Squantor/squantorDevelBoards/electronics/nuclone_STM32F031K6/README.md

# Nuclone development board for STM32F030K6
STM32F031K6 development board inspired by the nucleo series from STM32.
## TODO's
Still some things need to be done:
* schematic entry (WIP)
* PCB layout (Done)
* Review with one night in between (Done)
* Produce at [JLCPCB](https://jlcpcb.com/) (Done)
* Assemble (Done)
* Test & characterise (WIP)
* update Readme.md with pictures and BOM (WIP)
