Squantor/squantorDevelBoards/mechanical/small_nuclone_base_plate/README.md

# Small nuclone board box base plate
Base plate to mount the nuclone board on.
## Variants
* binding post holes for m3 screws
* binding post holes for m3 threaded inserts
## Pictures
TODO
