Squantor/squantorDevelBoards/electronics/nuclone_LPC1125JBD48-303/README.md

# Nuclone development board for LPC1125JBD48/303
LPC1125JBD48 development board inspired by the nucleo series from STM32.
## TODO's
Still some things need to be done:
* schematic entry (WIP)
* PCB layout (WIP)
* Review with one night in between (TODO)
* Produce at [JLCPCB](https://jlcpcb.com/) (TODO)
* Assemble (TODO)
* Test & characterise (TODO)
* update Readme.md with pictures and BOM (TODO)
