Squantor/squantorDevelBoards/software/cobalt_ant/README.md

# cobalt ant bringup
This is the bringup and test code for the cobalt ant datalogger. 
## TODO
* remove dependency on stdio and string libraries
* Some hardware pin definitions/libraries needed
