Squantor/squantorDevelBoards/electronics/nuclone_tester_medium/README.md

# Nuclone tester for medium sized boards
Test jig for the Medium sized nuclone boards.
## TODO's
Still some things need to be done:
* schematic entry (Done)
* PCB layout (Done)
* Review with one night in between (Wip)
* Produce at [JLCPCB](https://jlcpcb.com/) (TODO)
* Assemble (TODO)
* Test & characterise (TODO)
* update Readme.md with pictures and BOM (TODO)
