Squantor/squantorDevelBoards/electronics/nuclone_LPC804M101JHI33/nuclone_LPC804M101JHI33.kicad_pcb

## KiCad design electronics/nuclone_LPC804M101JHI33/nuclone_LPC804M101JHI33.kicad_pcb (2022-09-12)

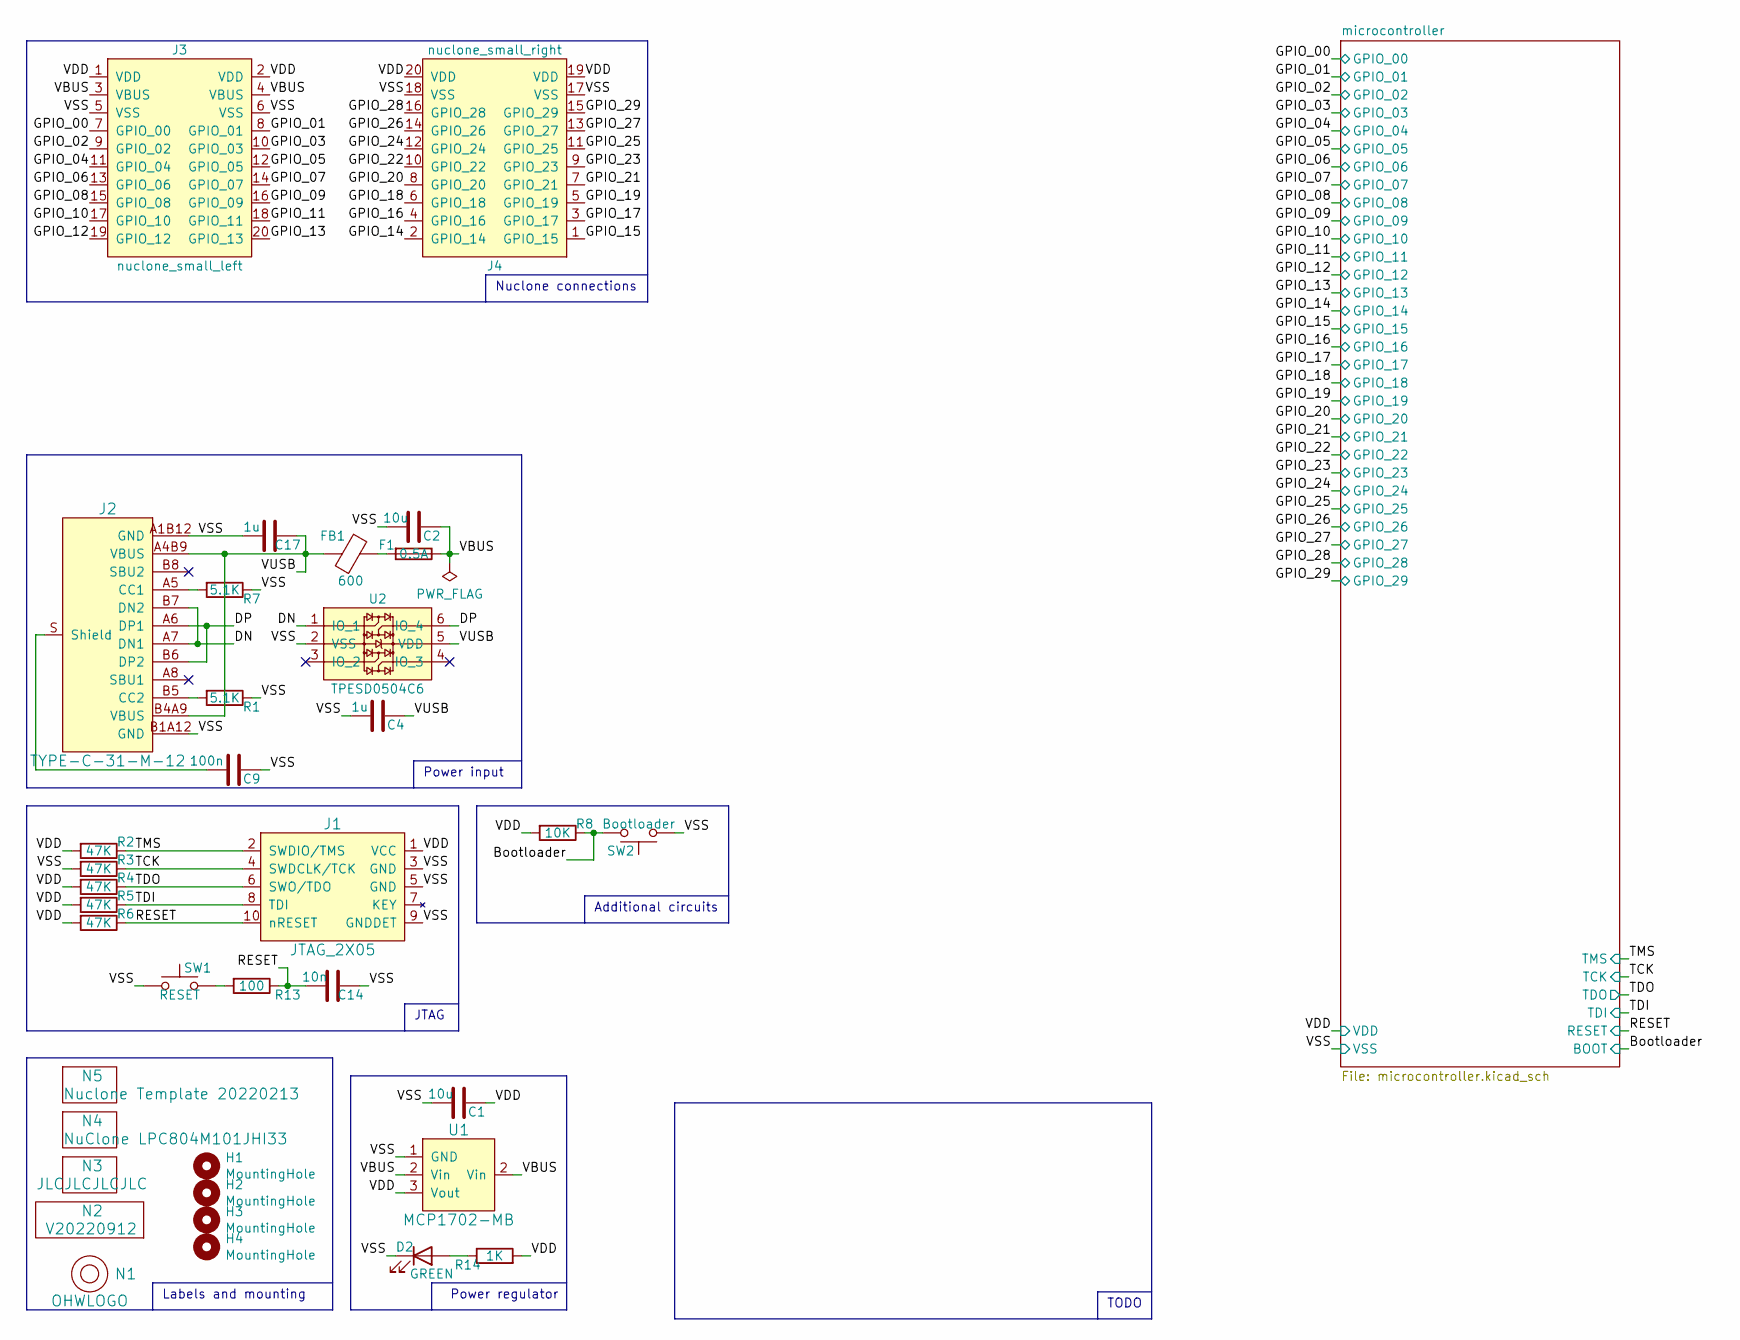
[picture p26: schematic nuclone_LPC804M101JHI33.kicad_sch]

Parts:
C1, C2: 10u; C_0603
C4: 1u; C_0402
C9: 100n; C_0805
C14: 10n; C_0402
C17: 1u; C_0603
D2: GREEN; LED_0603_hand
F1: 0.5A; F_0603_hand
FB1: 600; L_0603
H1, H2, H3, H4: MountingHole; MountingHole_3.2mm_M3_Pad_Via
J1: JTAG_2X05; Header-0127-2X05-H006
J2: TYPE-C-31-M-12; USB-C-HRO-31-M-12
J3: nuclone_small_left; nuclone_small_left_stacked
J4: nuclone_small_right; nuclone_small_right_stacked
N1: OHWLOGO; OSHW-Symbol_6.7x6mm_SilkScreen
N2: V20220912; Label_Generic
N3: JLCJLCJLCJLC; Label_Generic
N4: NuClone LPC804M101JHI33; Label_Generic
N5: Nuclone Template 20220213; Label_Generic
R1, R7: 5.1K; R_0402_hand
R2, R3, R4, R5, R6: 47K; R_0402_hand
R8: 10K; R_0402_hand
R13: 100; R_0402_hand
R14: 1K; R_0402_hand
SW1: RESET; TD-85XU
SW2: Bootloader; TD-85XU
U1: MCP1702-MB; SOT89-NXP
U2: TPESD0504C6; SOT363-ONsemi

Connections:
/Bootloader: R8.1, SW2.2; also elsewhere on the board
/DN: J2.A7 (DN1), J2.B7 (DN2), U2.1 (IO_1)
/DP: J2.A6 (DP1), J2.B6 (DP2), U2.6 (IO_4)
/GPIO_00: J3.7 (GPIO_00); also elsewhere on the board
/GPIO_01: J3.8 (GPIO_01); also elsewhere on the board
/GPIO_02: J3.9 (GPIO_02); also elsewhere on the board
/GPIO_03: J3.10 (GPIO_03); also elsewhere on the board
/GPIO_04: J3.11 (GPIO_04); also elsewhere on the board
/GPIO_05: J3.12 (GPIO_05); also elsewhere on the board
/GPIO_06: J3.13 (GPIO_06); also elsewhere on the board
/GPIO_07: J3.14 (GPIO_07); also elsewhere on the board
/GPIO_08: J3.15 (GPIO_08); also elsewhere on the board
/GPIO_09: J3.16 (GPIO_09); also elsewhere on the board
/GPIO_10: J3.17 (GPIO_10); also elsewhere on the board
/GPIO_11: J3.18 (GPIO_11); also elsewhere on the board
/GPIO_12: J3.19 (GPIO_12); also elsewhere on the board
/GPIO_13: J3.20 (GPIO_13); also elsewhere on the board
/GPIO_14: J4.2 (GPIO_14); also elsewhere on the board
/GPIO_15: J4.1 (GPIO_15); also elsewhere on the board
/GPIO_16: J4.4 (GPIO_16); also elsewhere on the board
/GPIO_17: J4.3 (GPIO_17); also elsewhere on the board
/GPIO_18: J4.6 (GPIO_18); also elsewhere on the board
/GPIO_19: J4.5 (GPIO_19); also elsewhere on the board
/GPIO_20: J4.8 (GPIO_20); also elsewhere on the board
/GPIO_21: J4.7 (GPIO_21); also elsewhere on the board
/GPIO_22: J4.10 (GPIO_22); also elsewhere on the board
/GPIO_23: J4.9 (GPIO_23); also elsewhere on the board
/GPIO_24: J4.12 (GPIO_24); also elsewhere on the board
/GPIO_25: J4.11 (GPIO_25); also elsewhere on the board
/GPIO_26: J4.14 (GPIO_26); also elsewhere on the board
/GPIO_27: J4.13 (GPIO_27); also elsewhere on the board
/GPIO_28: J4.16 (GPIO_28); also elsewhere on the board
/GPIO_29: J4.15 (GPIO_29); also elsewhere on the board
/RESET: C14.2, J1.10 (nRESET), R6.1, R13.1; also elsewhere on the board
/TCK: J1.4 (SWDCLK/TCK), R3.1; also elsewhere on the board
/TDI: J1.8 (TDI), R5.1
/TDO: J1.6 (SWO/TDO), R4.1
/TMS: J1.2 (SWDIO/TMS), R2.1; also elsewhere on the board
/VBUS: C2.2, F1.1, J3.3 (VBUS), J3.4 (VBUS), U1.2 (Vin)
/VDD: C1.1, J1.1 (VCC), J3.1 (VDD), J3.2 (VDD), J4.19 (VDD), J4.20 (VDD), R2.2, R4.2, R5.2, R6.2, R8.2, R14.2, U1.3 (Vout); also elsewhere on the board
/VSS: C1.2, C2.1, C4.2, C9.1, C14.1, C17.1, D2.1 (K), J1.3 (GND), J1.5 (GND), J1.9 (GNDDET), J2.A1B12 (GND), J2.B1A12 (GND), J3.5 (VSS), J3.6 (VSS), J4.17 (VSS), J4.18 (VSS), R1.1, R3.2, R7.1, SW1.1, SW2.1, U1.1 (GND), U2.2 (VSS); also elsewhere on the board
/VUSB: C4.1, C17.2, FB1.2, J2.A4B9 (VBUS), J2.B4A9 (VBUS), U2.5 (VDD)
unnamed: C9.2, J2.S (Shield)
unnamed: D2.2 (A), R14.1
unnamed: F1.2, FB1.1
unnamed: J2.A5 (CC1), R7.2
unnamed: J2.B5 (CC2), R1.2
unnamed: R13.2, SW1.2

Notes on the sheet:
Power input
Labels and mounting
Additional circuits
Nuclone connections
JTAG
TODO
Power regulator

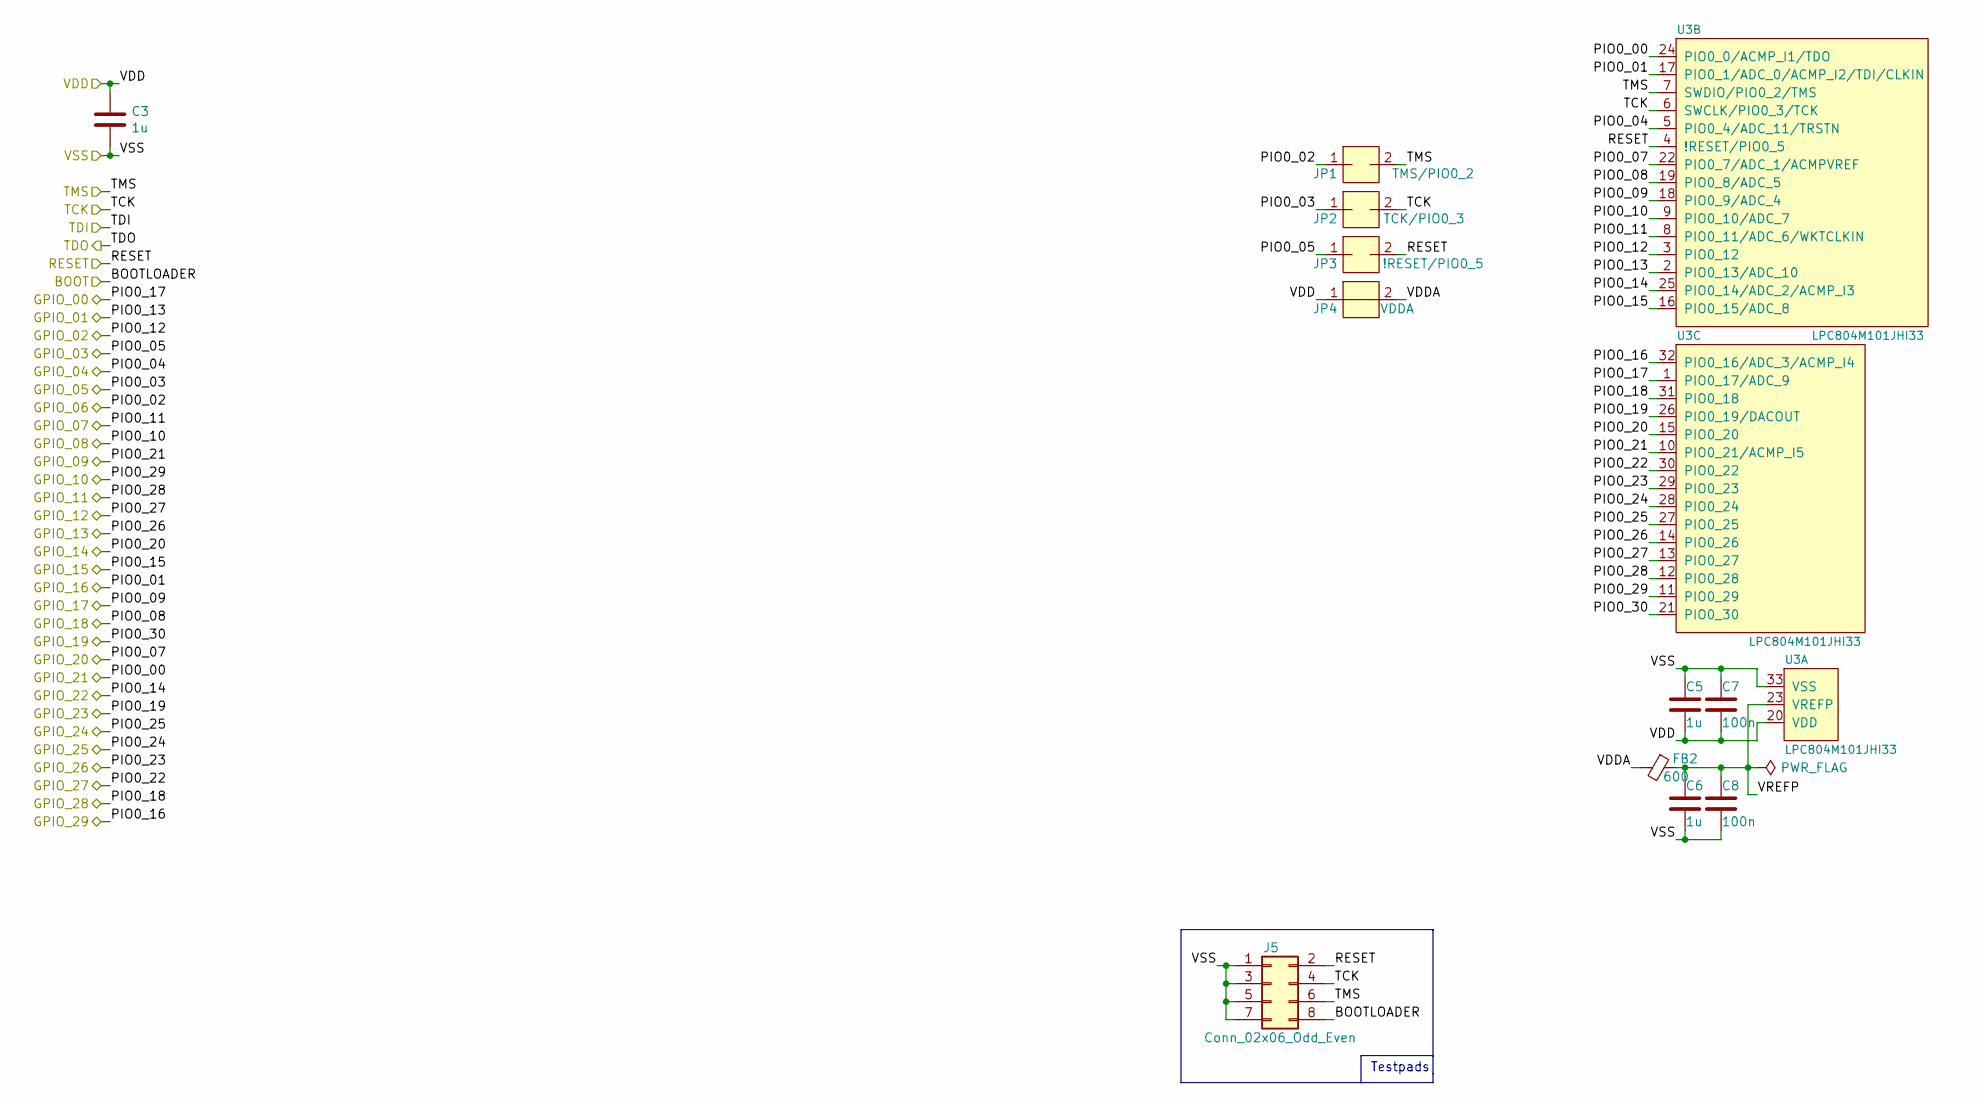
[picture p27: schematic microcontroller.kicad_sch]

Parts:
C3, C5, C6: 1u; C_0402
C7, C8: 100n; C_0402
FB2: 600; L_0402
J5: Conn_02x06_Odd_Even; Header-0127-2X04-H006
JP1: TMS/PIO0_2; solder_jumper_0402_2way_noconn
JP2: TCK/PIO0_3; solder_jumper_0402_2way_noconn
JP3: !RESET/PIO0_5; solder_jumper_0402_2way_noconn
JP4: VDDA; solder_jumper_0402_2way_conn
U3: LPC804M101JHI33; SOT617-3_alt_paste

Connections:
/Bootloader: J5.8; also elsewhere on the board
/GPIO_00: U3.1 (PIO0_17/ADC_9); also elsewhere on the board
/GPIO_01: U3.2 (PIO0_13/ADC_10); also elsewhere on the board
/GPIO_02: U3.3 (PIO0_12); also elsewhere on the board
/GPIO_03: JP3.1; also elsewhere on the board
/GPIO_04: U3.5 (PIO0_4/ADC_11/TRSTN); also elsewhere on the board
/GPIO_05: JP2.1; also elsewhere on the board
/GPIO_06: JP1.1; also elsewhere on the board
/GPIO_07: U3.8 (PIO0_11/ADC_6/WKTCLKIN); also elsewhere on the board
/GPIO_08: U3.9 (PIO0_10/ADC_7); also elsewhere on the board
/GPIO_09: U3.10 (PIO0_21/ACMP_I5); also elsewhere on the board
/GPIO_10: U3.11 (PIO0_29); also elsewhere on the board
/GPIO_11: U3.12 (PIO0_28); also elsewhere on the board
/GPIO_12: U3.13 (PIO0_27); also elsewhere on the board
/GPIO_13: U3.14 (PIO0_26); also elsewhere on the board
/GPIO_14: U3.15 (PIO0_20); also elsewhere on the board
/GPIO_15: U3.16 (PIO0_15/ADC_8); also elsewhere on the board
/GPIO_16: U3.17 (PIO0_1/ADC_0/ACMP_I2/TDI/CLKIN); also elsewhere on the board
/GPIO_17: U3.18 (PIO0_9/ADC_4); also elsewhere on the board
/GPIO_18: U3.19 (PIO0_8/ADC_5); also elsewhere on the board
/GPIO_19: U3.21 (PIO0_30); also elsewhere on the board
/GPIO_20: U3.22 (PIO0_7/ADC_1/ACMPVREF); also elsewhere on the board
/GPIO_21: U3.24 (PIO0_0/ACMP_I1/TDO); also elsewhere on the board
/GPIO_22: U3.25 (PIO0_14/ADC_2/ACMP_I3); also elsewhere on the board
/GPIO_23: U3.26 (PIO0_19/DACOUT); also elsewhere on the board
/GPIO_24: U3.27 (PIO0_25); also elsewhere on the board
/GPIO_25: U3.28 (PIO0_24); also elsewhere on the board
/GPIO_26: U3.29 (PIO0_23); also elsewhere on the board
/GPIO_27: U3.30 (PIO0_22); also elsewhere on the board
/GPIO_28: U3.31 (PIO0_18); also elsewhere on the board
/GPIO_29: U3.32 (PIO0_16/ADC_3/ACMP_I4); also elsewhere on the board
/RESET: J5.2, JP3.2, U3.4 (!RESET/PIO0_5); also elsewhere on the board
/TCK: J5.4, JP2.2, U3.6 (SWCLK/PIO0_3/TCK); also elsewhere on the board
/TMS: J5.6, JP1.2, U3.7 (SWDIO/PIO0_2/TMS); also elsewhere on the board
/VDD: C3.1, C5.2, C7.2, JP4.1, U3.20 (VDD); also elsewhere on the board
/VSS: C3.2, C5.1, C6.2, C7.1, C8.2, J5.1, J5.3, J5.5, J5.7, U3.33 (VSS); also elsewhere on the board
/microcontroller/VDDA: FB2.2, JP4.2
/microcontroller/VREFP: C6.1, C8.1, FB2.1, U3.23 (VREFP)

Notes on the sheet:
Testpads

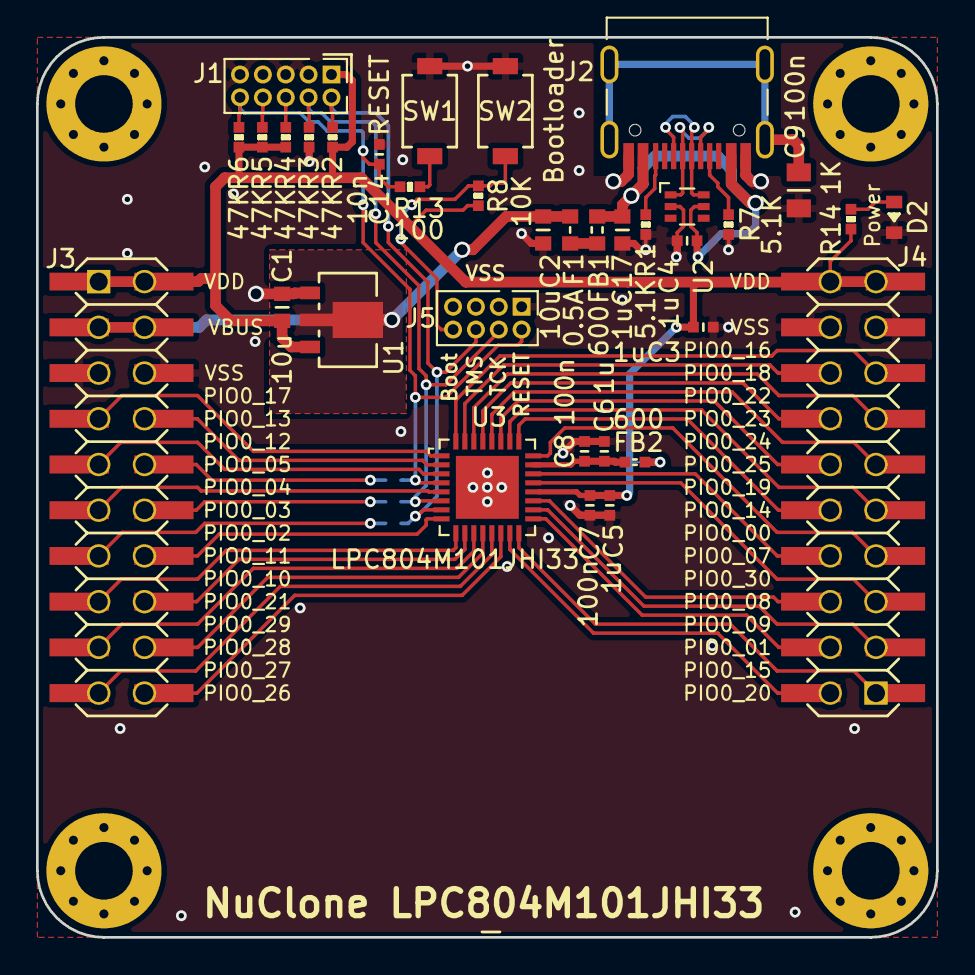
[picture p28: board nuclone_LPC804M101JHI33.kicad_pcb from above]

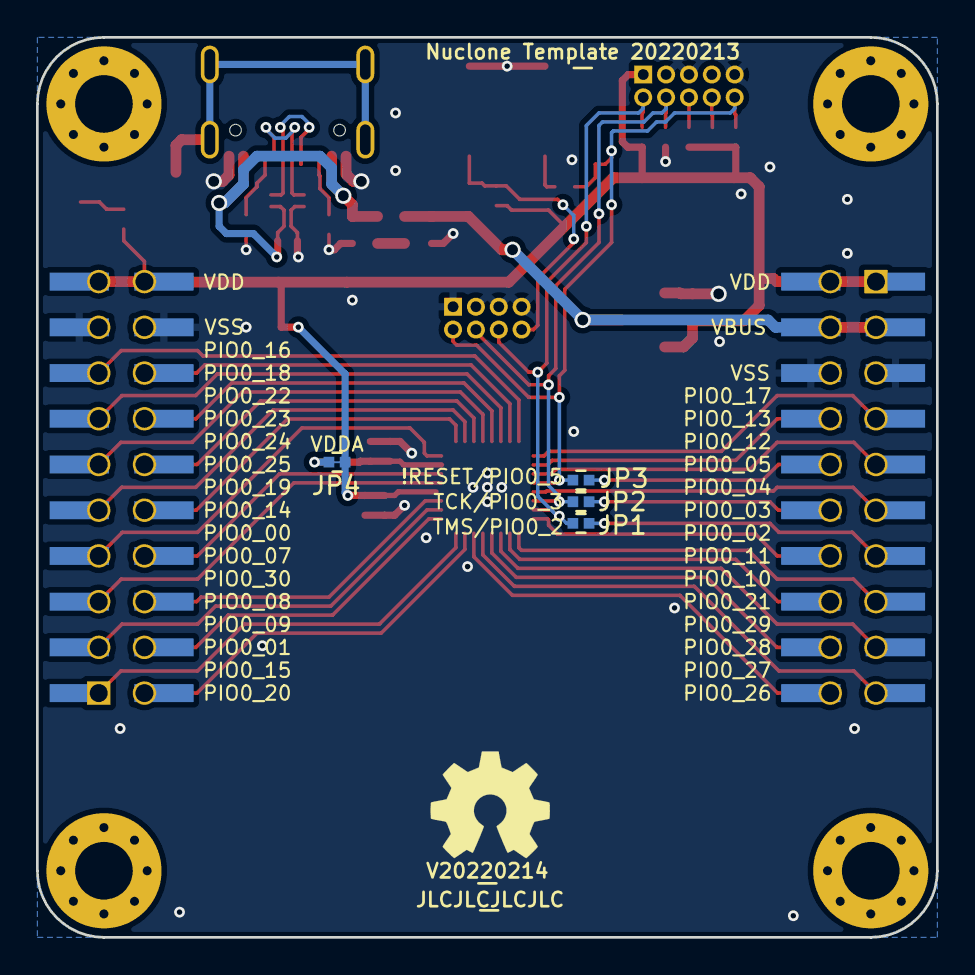
[picture p29: board nuclone_LPC804M101JHI33.kicad_pcb from below]

Board: 2 copper layers, 50.0 x 50.0 mm, 48 parts (8 on the bottom side), 50 nets.
