Squantor/squantorDevelBoards/electronics/nuclone_LPC1114JBD48/nuclone_LPC1114JBD48.kicad_pcb

## KiCad design electronics/nuclone_LPC1114JBD48/nuclone_LPC1114JBD48.kicad_pcb (2022-05-29)

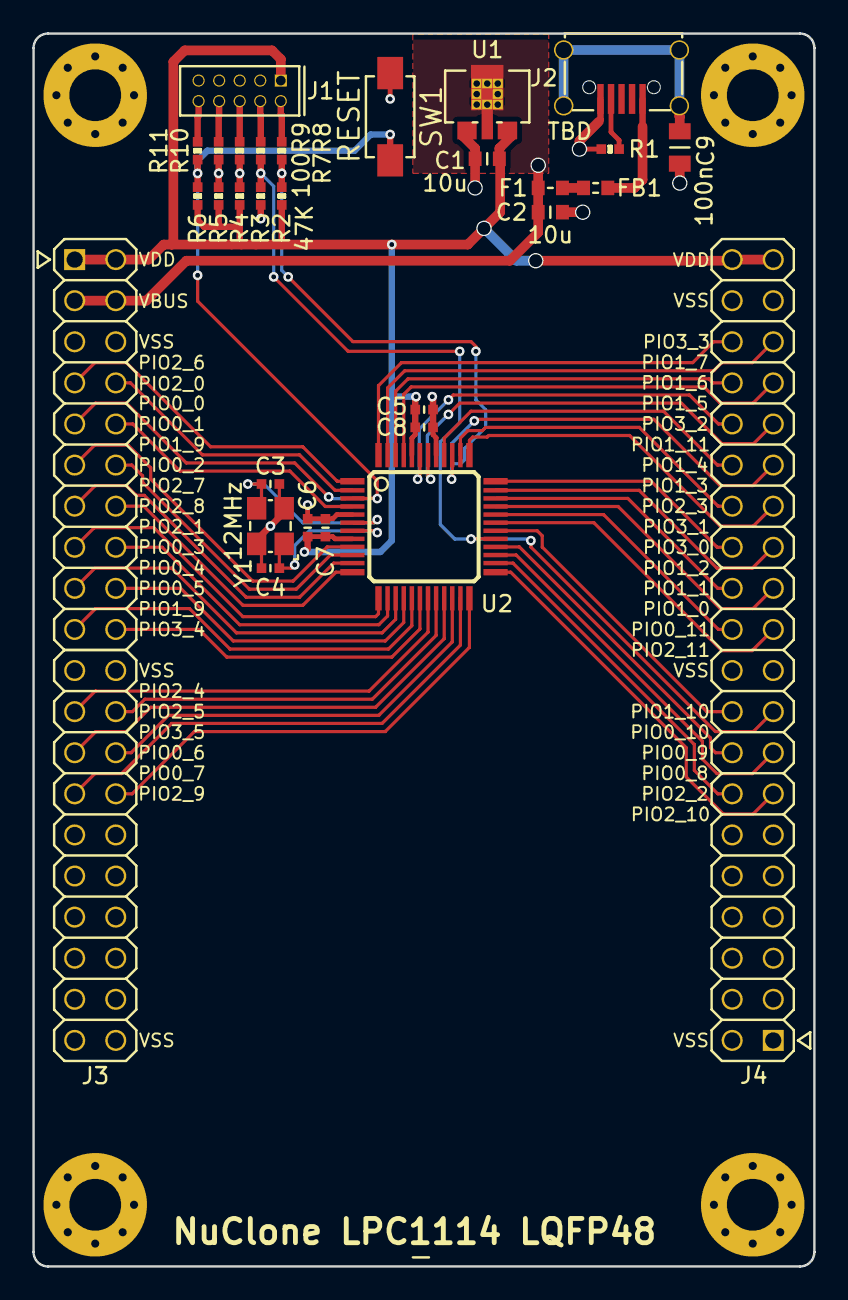
[picture p30: board nuclone_LPC1114JBD48.kicad_pcb from above]

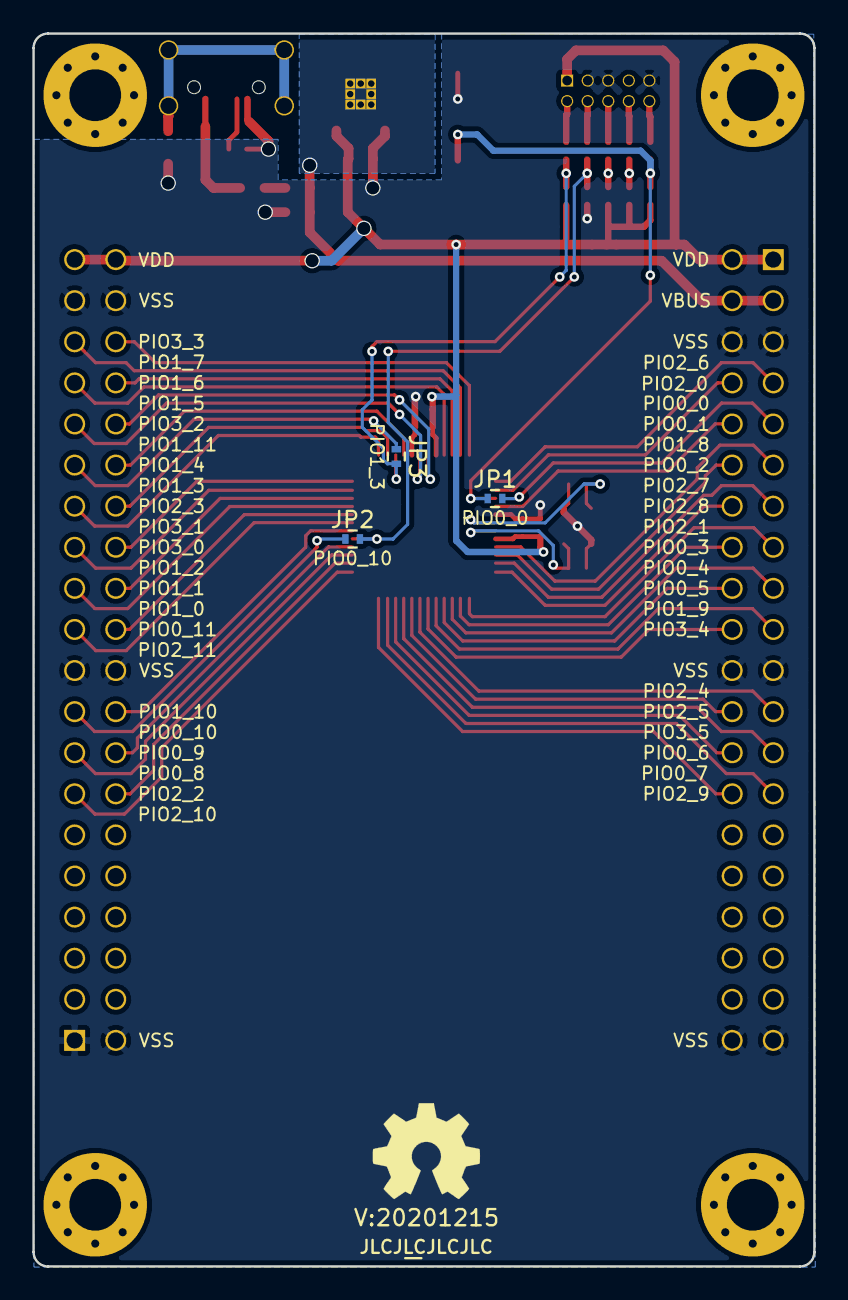
[picture p31: board nuclone_LPC1114JBD48.kicad_pcb from below]

Board: 2 copper layers, 48.3 x 76.2 mm, 41 parts (6 on the bottom side), 61 nets.

Parts:
C1, C2: 10u; C_0603
C3, C4: 12p; C_0402
C5, C6: 1u; C_0402
C7, C8: 100n; C_0402
C9: 100n; C_0805
F1: 0.5A; F_0603_hand
FB1: 100; L_0603
H1, H2, H3, H4: MountingHole; MountingHole_3.2mm_M3_Pad_Via
J1: JTAG_2X05; Header-0127-2X05-H006
J2: USB-ID; USB-muB-SMD_TH
J3: nuclone_small_left; nuclone_medium_left
J4: nuclone_small_right; nuclone_medium_right
JP1: PIO0_0; solder_jumper_2way_noconn
JP2: PIO0_10; solder_jumper_2way_noconn
JP3: PIO1_3; solder_jumper_2way_noconn
N1: OHWLOGO; OSHW-Symbol_6.7x6mm_SilkScreen
N2: 20201215; Label_version
N3: JLCJLCJLCJLC; Label_Generic
N4: NuClone LPC1114 LQFP48; Label_Generic
R1: TBD; R_0402_hand
R2, R3, R4, R5, R6: 47K; R_0402_hand
R7, R8, R9, R10, R11: 100; R_0402_hand
SW1: RESET; DTSM3
U1: MCP1702-MB; SOT89-SOT23-Dual-NXP
U2: LPC1114FBD48_302; SOT313-2-NXP
Y1: 12MHz; Crystal_3225_4

Connections:
/PIO0_0: J3.9 (GPIO_02), JP1.1
/PIO0_1: J3.10 (GPIO_03), U2.4 (PIO0_1/CLKOUT/CT32B0_MAT2)
/PIO0_2: J3.12 (GPIO_05), U2.10 (PIO0_2/SSEL0/CT16B0_CAP0)
/PIO0_3: J3.16 (GPIO_09), U2.14 (PIO0_3)
/PIO0_4: J3.17 (GPIO_10), U2.15 (PIO0_4/SCL)
/PIO0_5: J3.18 (GPIO_11), U2.16 (PIO0_5/SDA)
/PIO0_6: J3.26 (GPIO_17), U2.22 (PIO0_6/SCK0)
/PIO0_7: J3.27 (GPIO_18), U2.23 (PIO0_7/CTS)
/PIO0_8: J4.26 (GPIO_50), U2.27 (PIO0_8/MISO0/CT16B0_MAT0)
/PIO0_9: J4.25 (GPIO_51), U2.28 (PIO0_9/MOSI0/CT16B0_MAT1)
/PIO0_10: J4.24 (GPIO_48), JP2.1
/PIO0_11: J4.19 (VSS), U2.32 (R/PIO0_11/AD0/CT32B0_MAT3)
/PIO1_0: J4.18 (GPIO_44), U2.33 (R/PIO1_0/AD1/CT32B1_CAP0)
/PIO1_1: J4.17 (GPIO_45), U2.34 (R/PIO1_1/AD2/CT32B1_MAT0)
/PIO1_2: J4.16 (GPIO_42), U2.35 (R/PIO1_2/AD3/CT32B1_MAT1)
/PIO1_3: J4.12 (GPIO_38), JP3.1
/PIO1_4: J4.11 (GPIO_39), U2.40 (PIO1_4/AD5/CT32B1_MAT3/WAKEUP)
/PIO1_5: J4.8 (GPIO_34), U2.45 (PIO1_5/RTS/CT32B0_CAP0)
/PIO1_6: J4.7 (GPIO_35), U2.46 (PIO1_6/RXD/CT32B0_MAT0)
/PIO1_7: J4.6 (GPIO_32), U2.47 (PIO1_7/TXD/CT32B0_MAT1)
/PIO1_8: J3.11 (GPIO_04), U2.9 (PIO1_8/CT16B1_CAP0)
/PIO1_9: J3.19 (GPIO_12), U2.17 (PIO1_9/CT16B1_MAT0)
/PIO1_10: J4.23 (GPIO_49), U2.30 (PIO1_10/AD6/CT16B1_MAT1)
/PIO1_11: J4.10 (GPIO_36), U2.42 (PIO1_11/AD7)
/PIO2_0: J3.8 (GPIO_01), U2.2 (PIO2_0/DTR/SSEL1)
/PIO2_1: J3.15 (GPIO_08), U2.13 (PIO2_1/DSR/SCK1)
/PIO2_2: J4.27 (GPIO_53), U2.26 (PIO2_2/DCD/MISO1)
/PIO2_3: J4.13 (GPIO_41), U2.38 (PIO2_3/RI/MOSI1)
/PIO2_4: J3.23 (GPIO_14), U2.19 (PIO2_4)
/PIO2_5: J3.24 (GPIO_15), U2.20 (PIO2_5)
/PIO2_6: J3.7 (GPIO_00), U2.1 (PIO2_6)
/PIO2_7: J3.13 (GPIO_06), U2.11 (PIO2_7)
/PIO2_8: J3.14 (GPIO_07), U2.12 (PIO2_8)
/PIO2_9: J3.28 (GPIO_19), U2.24 (PIO2_9)
/PIO2_10: J4.28 (GPIO_52), U2.25 (PIO2_10)
/PIO2_11: J4.20 (VSS), U2.31 (PIO2_11/SCK0)
/PIO3_0: J4.15 (GPIO_43), U2.36 (PIO3_0/DTR)
/PIO3_1: J4.14 (GPIO_40), U2.37 (PIO3_1/DSR)
/PIO3_2: J4.9 (GPIO_37), U2.43 (PIO3_2/DCD)
/PIO3_3: J4.5 (GPIO_33), U2.48 (PIO3_3/RI)
/PIO3_4: J3.20 (GPIO_13), U2.18 (PIO3_4)
/PIO3_5: J3.25 (GPIO_16), U2.21 (PIO3_5)
/RESET: JP1.2, R6.1, R11.2, SW1.2, U2.3 (RESET/PIO0_0)
/TCK: JP2.2, R3.1, R8.2, U2.29 (SWCLK/PIO0_10/SCK0/CT16B0_MAT2)
/TDI: R5.1, R10.2
/TDO: R4.1, R9.2
/TMS: JP3.2, R2.1, R7.2, U2.39 (SWDIO/PIO1_3/AD4/CT32B1_MAT2)
/VBUS: C2.2, F1.1, J3.3 (VBUS), J3.4 (VBUS), U1.2 (Vin)
/VDD: C1.1, C5.1, C6.1, C7.1, C8.1, J1.1 (VCC), J3.1 (VDD), J3.2 (VDD), J4.1 (VSS), J4.2 (VSS), R2.2, R4.2, R5.2, R6.2, U1.3 (Vout), U2.8 (VDD), U2.44 (VDD)
/VSS: C1.2, C2.1, C3.2, C4.2, C5.2, C6.2, C7.2, C8.2, C9.1, J1.3 (GND), J1.5 (GND), J1.9 (GNDDET), J2.5 (GND), J3.5 (VSS), J3.6 (VSS), J3.21 (VSS), J3.22 (VSS), J3.39 (VSS), J3.40 (VSS), J4.3 (GPIO_31), J4.4 (GPIO_30), J4.21 (GPIO_47), J4.22 (GPIO_46), J4.39 (VDD), J4.40 (VDD), R1.1, R3.2, SW1.1, U1.1 (GND), U2.5 (VSS), U2.41 (VSS), Y1.2, Y1.4
unnamed: C3.1, U2.6 (XTALIN), Y1.3
unnamed: C4.1, U2.7 (XTALOUT), Y1.1
unnamed: C9.2, J2.S (Shield)
unnamed: F1.2, FB1.1
unnamed: J1.2 (SWDIO/TMS), R7.1
unnamed: J1.4 (SWDCLK/TCK), R8.1
unnamed: J1.6 (SWO/TDO), R9.1
unnamed: J1.8 (TDI), R10.1
unnamed: J1.10 (nRESET), R11.1
unnamed: FB1.2, J2.1 (VBUS)
unnamed: J2.4 (ID), R1.2
