Squantor/squantorDevelBoards/electronics/nuclone_LPC824M201JDH20/nuclone_LPC824M201JDH20.kicad_pcb

## KiCad design electronics/nuclone_LPC824M201JDH20/nuclone_LPC824M201JDH20.kicad_pcb (2022-05-29)

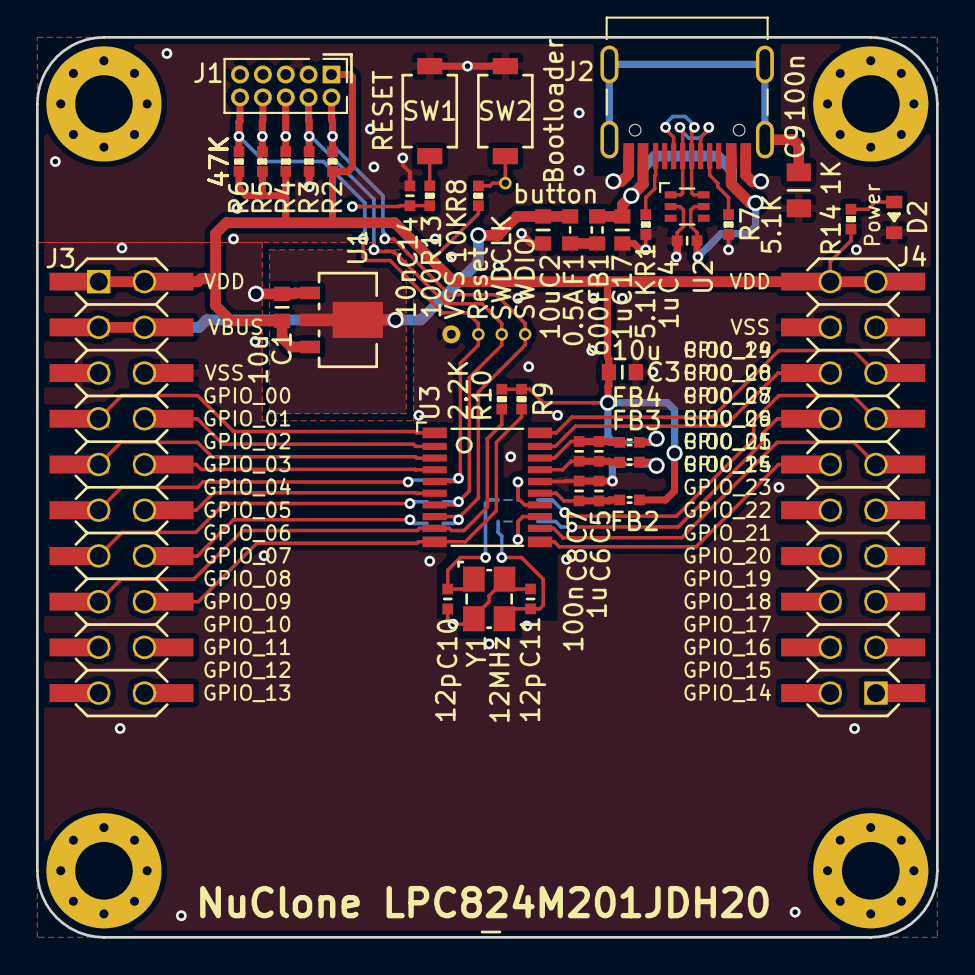
[picture p32: board nuclone_LPC824M201JDH20.kicad_pcb from above]

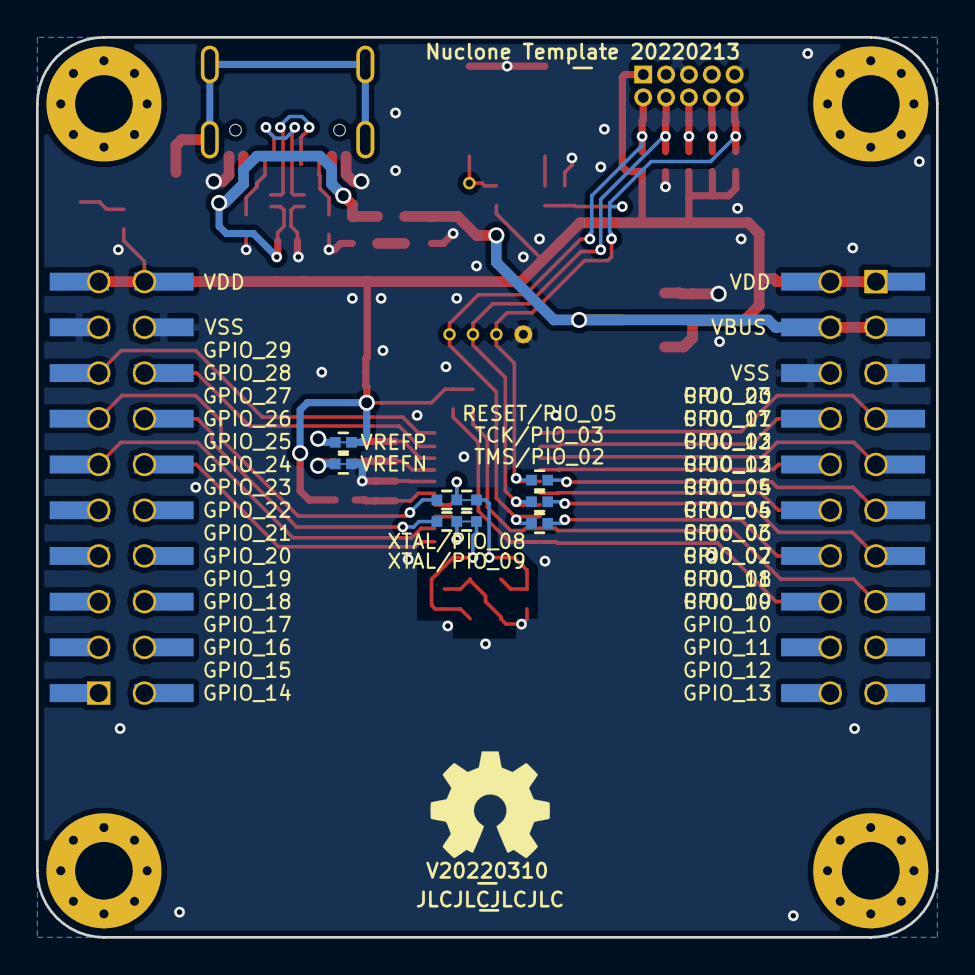
[picture p33: board nuclone_LPC824M201JDH20.kicad_pcb from below]

Board: 2 copper layers, 50.0 x 50.0 mm, 62 parts (11 on the bottom side), 43 nets.

Parts:
C1, C2, C3: 10u; C_0603
C4, C5, C6: 1u; C_0402
C7, C8: 100n; C_0402
C9: 100n; C_0805
C10, C11: 12p; C_0402
C14: 10n; C_0402
C17: 1u; C_0603
D2: GREEN; LED_0603_hand
F1: 0.5A; F_0603_hand
FB1: 600; L_0603
FB2, FB3, FB4: 600; L_0402
H1, H2, H3, H4: MountingHole; MountingHole_3.2mm_M3_Pad_Via
J1: JTAG_2X05; Header-0127-2X05-H006
J2: TYPE-C-31-M-12; USB-C-HRO-31-M-12
J3: nuclone_small_left; nuclone_small_left_stacked
J4: nuclone_small_right; nuclone_small_right_stacked
JP1: TMS/PIO_02; solder_jumper_0402_2way_noconn
JP2: TCK/PIO_03; solder_jumper_0402_2way_noconn
JP3: RESET/PIO_05; solder_jumper_0402_2way_noconn
JP4: VREFP; solder_jumper_0402_2way_conn
JP5: VREFN; solder_jumper_0402_2way_conn
JP6: XTAL/PIO_08; solder_jumper_0402_3way_12conn
JP7: XTAL/PIO_09; solder_jumper_0402_3way_12conn
N1: OHWLOGO; OSHW-Symbol_6.7x6mm_SilkScreen
N2: V20220310; Label_Generic
N3: JLCJLCJLCJLC; Label_Generic
N4: NuClone LPC824M201JDH20; Label_Generic
N5: Nuclone Template 20220213; Label_Generic
R1, R7: 5.1K; R_0402_hand
R2, R3, R4, R5, R6: 47K; R_0402_hand
R8: 10K; R_0402_hand
R9, R10: 2.2K; R_0402_hand
R13: 100; R_0402_hand
R14: 1K; R_0402_hand
SW1: RESET; TD-85XU
SW2: Bootloader; TD-85XU
TP1: SWDIO; TestPoint_hole_H04R07
TP2: SWDCLK; TestPoint_hole_H04R07
TP3: VSS; TestPoint_hole_H05R10
TP4: button; TestPoint_hole_H04R07
TP5: Reset; TestPoint_hole_H04R07
U1: MCP1702-MB; SOT89-NXP
U2: TPESD0504C6; SOT363-ONsemi
U3: LPC824M201JDH20; SOT360-NXP
Y1: 12MHz; Crystal_3225_4

Connections:
/Bootloader: R8.1, SW2.2, TP4.1
/DN: J2.A7 (DN1), J2.B7 (DN2), U2.1 (IO_1)
/DP: J2.A6 (DP1), J2.B6 (DP2), U2.6 (IO_4)
/GPIO_00: J3.7 (GPIO_00), U3.1 (PIO0_23/ADC_3/ACMP_I4)
/GPIO_01: J3.8 (GPIO_01), U3.2 (PIO0_17/ADC_9)
/GPIO_02: J3.9 (GPIO_02), U3.3 (PIO0_13/ADC_10)
/GPIO_03: J3.10 (GPIO_03), U3.4 (PIO0_12)
/GPIO_04: J3.11 (GPIO_04), JP3.2
/GPIO_05: J3.12 (GPIO_05), U3.6 (PIO0_4/ADC_11/WAKEUP/TRST)
/GPIO_06: J3.13 (GPIO_06), JP2.2
/GPIO_07: J3.14 (GPIO_07), JP1.2
/GPIO_08: J3.15 (GPIO_08), R10.2, U3.9 (PIO0_11/I2C0_SDA)
/GPIO_09: J3.16 (GPIO_09), R9.2, U3.10 (PIO0_10/I2C0_SCL)
/GPIO_24: J4.12 (GPIO_24), U3.11 (PIO0_15)
/GPIO_25: J4.11 (GPIO_25), U3.12 (PIO0_1/ACMP_I2/CLKIN/TDI)
/GPIO_26: J4.14 (GPIO_26), JP7.3
/GPIO_27: J4.13 (GPIO_27), JP6.3
/GPIO_28: J4.16 (GPIO_28), U3.19 (PIO0_0/ACMP_I1/TDO)
/GPIO_29: J4.15 (GPIO_29), U3.20 (PIO0_14/ADC_2/ACMP_I3)
/RESET: C14.2, J1.10 (nRESET), JP3.1, R6.1, R13.1, TP5.1, U3.5 (RESET/PIO0_5)
/TCK: J1.4 (SWDCLK/TCK), JP2.1, R3.1, TP2.1, U3.7 (SWCLK/PIO0_3/TCK)
/TDI: J1.8 (TDI), R5.1
/TDO: J1.6 (SWO/TDO), R4.1
/TMS: J1.2 (SWDIO/TMS), JP1.1, R2.1, TP1.1, U3.8 (SWDIO/PIO0_2/TMS)
/VBUS: C2.2, F1.1, J3.3 (VBUS), J3.4 (VBUS), U1.2 (Vin)
/VDD: C1.1, C3.1, FB2.2, J1.1 (VCC), J3.1 (VDD), J3.2 (VDD), J4.19 (VDD), J4.20 (VDD), JP4.1, R2.2, R4.2, R5.2, R6.2, R8.2, R9.1, R10.1, R14.2, U1.3 (Vout)
/VSS: C1.2, C2.1, C3.2, C4.2, C5.2, C7.2, C9.1, C10.2, C11.2, C14.1, C17.1, D2.1 (K), J1.3 (GND), J1.5 (GND), J1.9 (GNDDET), J2.A1B12 (GND), J2.B1A12 (GND), J3.5 (VSS), J3.6 (VSS), J4.17 (VSS), J4.18 (VSS), JP5.1, R1.1, R3.2, R7.1, SW1.1, SW2.1, TP3.1, U1.1 (GND), U2.2 (VSS), U3.16 (VSS), Y1.2, Y1.4
/VUSB: C4.1, C17.2, FB1.2, J2.A4B9 (VBUS), J2.B4A9 (VBUS), U2.5 (VDD)
/microcontroller/VDDA: FB3.2, JP4.2
/microcontroller/VSSA: FB4.2, JP5.2
/microcontroller/XTALIN: JP6.2, U3.14 (PIO0_8/XTALIN)
/microcontroller/XTALOUT: JP7.2, U3.13 (PIO0_9/XTALOUT)
unnamed: C5.1, C7.1, FB2.1, U3.15 (VDD)
unnamed: C6.1, C8.1, FB3.1, U3.18 (VREFP)
unnamed: C6.2, C8.2, FB4.1, U3.17 (VREFN)
unnamed: C9.2, J2.S (Shield)
unnamed: C10.1, JP6.1, Y1.1
unnamed: C11.1, JP7.1, Y1.3
unnamed: D2.2 (A), R14.1
unnamed: F1.2, FB1.1
unnamed: J2.A5 (CC1), R7.2
unnamed: J2.B5 (CC2), R1.2
unnamed: R13.2, SW1.2
