Squantor/squantorDevelBoards/electronics/nuclone_LPC844M201BD64/nuclone_LPC844M201BD64.kicad_pcb

## KiCad design electronics/nuclone_LPC844M201BD64/nuclone_LPC844M201BD64.kicad_pcb (2022-05-29)

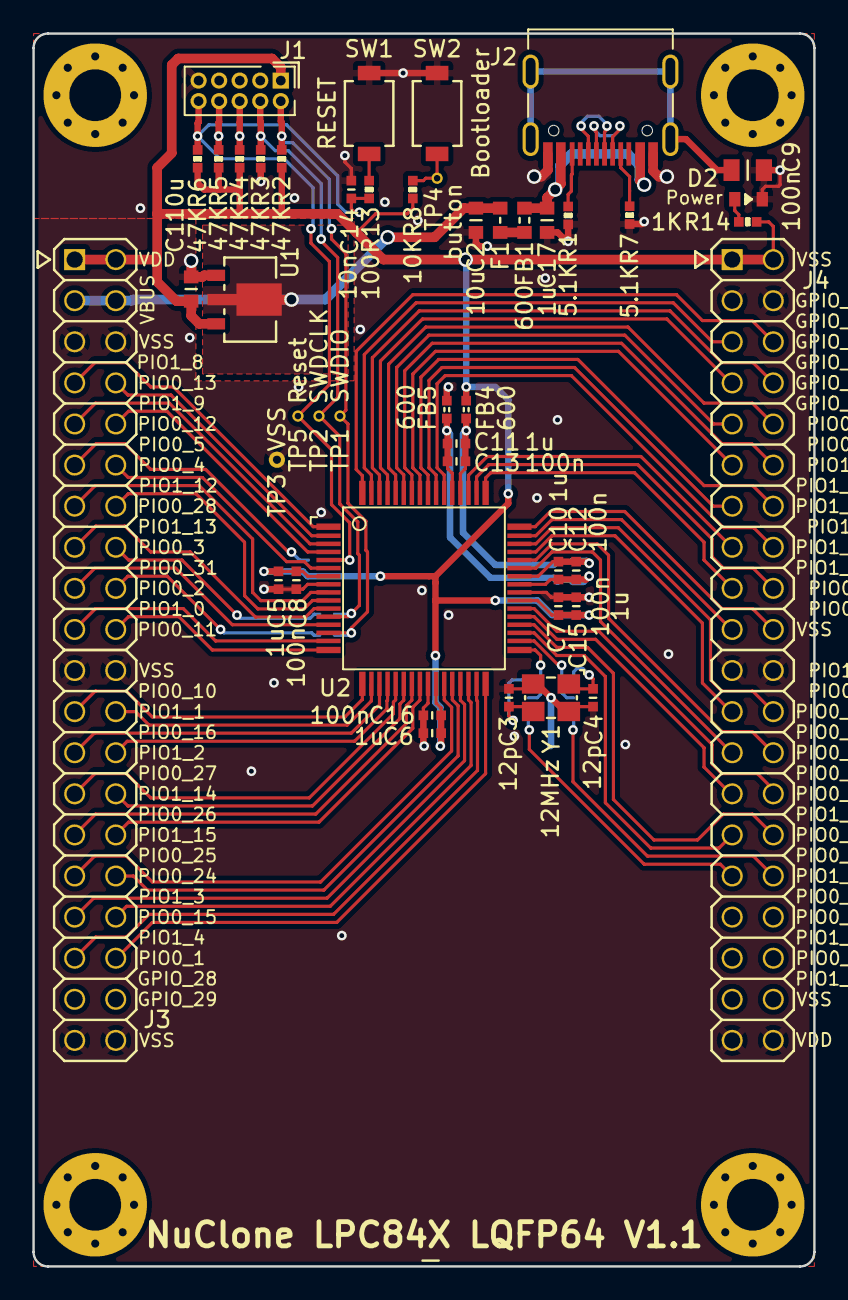
[picture p34: board nuclone_LPC844M201BD64.kicad_pcb from above]

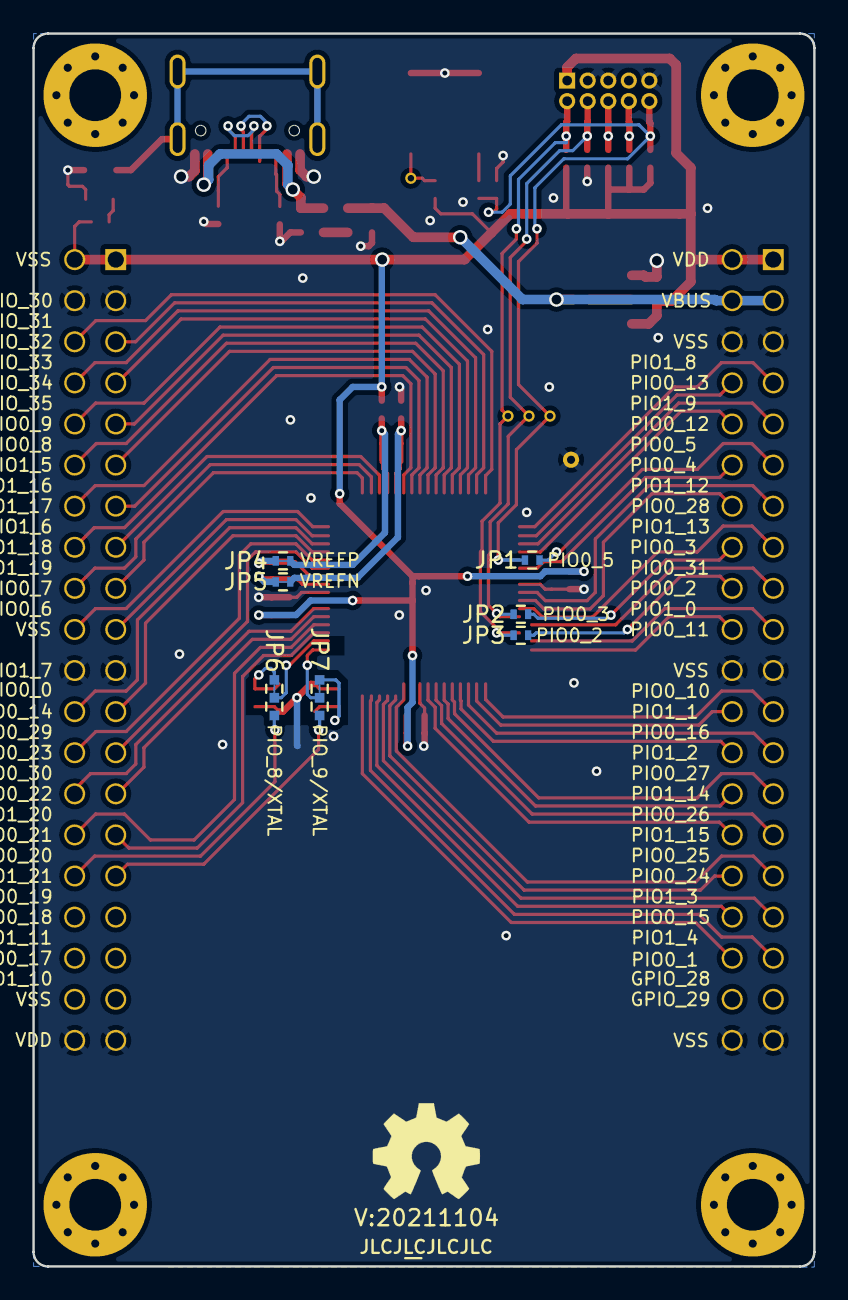
[picture p35: board nuclone_LPC844M201BD64.kicad_pcb from below]

Board: 2 copper layers, 48.3 x 76.2 mm, 61 parts (10 on the bottom side), 80 nets.

Parts:
C1, C2: 10u; C_0603
C3, C4: 12p; C_0402
C5, C6, C10, C11, C15: 1u; C_0402
C7, C8, C12, C13, C16: 100n; C_0402
C9: 100n; C_0805
C14: 10n; C_0402
C17: 1u; C_0603
D2: GREEN; LED_0603_hand
F1: 0.5A; F_0603_hand
FB1: 600; L_0603
FB4, FB5: 600; L_0402
H1, H2, H3, H4: MountingHole; MountingHole_3.2mm_M3_Pad_Via
J1: JTAG_2X05; Header-0127-2X05-H006
J2: TYPE-C-31-M-12; USB-C-HRO-31-M-12
J3: nuclone_small_left; nuclone_medium_left
J4: nuclone_small_right; nuclone_medium_right
JP1: PIO0_5; solder_jumper_2way_noconn
JP2: PIO0_3; solder_jumper_2way_noconn
JP3: PIO0_2; solder_jumper_2way_noconn
JP4: VREFP; solder_jumper_2way_conn
JP5: VREFN; solder_jumper_2way_conn
JP6: PIO_8/XTAL; solder_jumper_3way_12conn
JP7: PIO_9/XTAL; solder_jumper_3way_12conn
N1: OHWLOGO; OSHW-Symbol_6.7x6mm_SilkScreen
N2: 20211104; Label_version
N3: JLCJLCJLCJLC; Label_Generic
N4: NuClone LPC84X LQFP64 V1.1; Label_Generic
R1, R7: 5.1K; R_0402_hand
R2, R3, R4, R5, R6: 47K; R_0402_hand
R8: 10K; R_0402_hand
R13: 100; R_0402_hand
R14: 1K; R_0402_hand
SW1: RESET; TD-85XU
SW2: Bootloader; TD-85XU
TP1: SWDIO; TestPoint_hole_H04R07
TP2: SWDCLK; TestPoint_hole_H04R07
TP3: VSS; TestPoint_hole_H05R10
TP4: button; TestPoint_hole_H04R07
TP5: Reset; TestPoint_hole_H04R07
U1: MCP1702-MB; SOT89-NXP
U2: LPC845M301BD64; SOT314-2
Y1: 12MHz; Crystal_3225_4

Connections:
/Bootloader: R8.1, SW2.2, TP4.1
/PIO0_0: J4.20 (VSS), U2.48 (PIO0_0/ACMP_I1/TDO)
/PIO0_1: J3.36 (GPIO_27), U2.32 (PIO0_1/ACMP_I2/CLKIN/TDI)
/PIO0_2: J3.18 (GPIO_11), JP3.1
/PIO0_3: J3.16 (GPIO_09), JP2.1
/PIO0_4: J3.12 (GPIO_05), U2.6 (PIO0_4/ADC_11/TRSTN/WAKEUP)
/PIO0_5: J3.11 (GPIO_04), JP1.1
/PIO0_6: J4.24 (GPIO_48), U2.46 (PIO0_6/ADC_1/ACMPVREF)
/PIO0_7: J4.23 (GPIO_49), U2.45 (PIO0_7/ADC_0)
/PIO0_8: J4.32 (GPIO_56), JP6.3
/PIO0_8_I: JP6.2, U2.34 (PIO0_8/XTALIN)
/PIO0_9: J4.31 (GPIO_57), JP7.3
/PIO0_9_I: JP7.2, U2.33 (PIO0_9/XTALOUT)
/PIO0_10: J3.23 (GPIO_14), U2.17 (PIO0_10/I2C0_SCL_)
/PIO0_11: J3.20 (GPIO_13), U2.16 (PIO0_11/I2C0_SDA)
/PIO0_12: J3.10 (GPIO_03), U2.4 (PIO0_12)
/PIO0_13: J3.8 (GPIO_01), U2.2 (PIO0_13/ADC_10)
/PIO0_14: J4.17 (GPIO_45), U2.49 (PIO0_14/ACMP_I3/ADC_2)
/PIO0_15: J3.34 (GPIO_25), U2.30 (PIO0_15)
/PIO0_16: J3.25 (GPIO_16), U2.19 (PIO0_16)
/PIO0_17: J4.5 (GPIO_33), U2.63 (PIO0_17/ADC_9/DACOUT_0)
/PIO0_18: J4.7 (GPIO_35), U2.61 (PIO0_18/ADC_8)
/PIO0_19: J4.10 (GPIO_36), U2.60 (PIO0_19/ADC_7)
/PIO0_20: J4.12 (GPIO_38), U2.58 (PIO0_20/ADC_6)
/PIO0_21: J4.11 (GPIO_39), U2.57 (PIO0_21/ADC_5)
/PIO0_22: J4.13 (GPIO_41), U2.55 (PIO0_22/ADC_4)
/PIO0_23: J4.15 (GPIO_43), U2.51 (PIO0_23/ADC_3/ACMP_I4)
/PIO0_24: J3.32 (GPIO_23), U2.28 (PIO0_24)
/PIO0_25: J3.31 (GPIO_22), U2.27 (PIO0_25)
/PIO0_26: J3.29 (GPIO_20), U2.23 (PIO0_26)
/PIO0_27: J3.27 (GPIO_18), U2.21 (PIO0_27)
/PIO0_28: J3.14 (GPIO_07), U2.10 (PIO0_28/WKTCLKIN)
/PIO0_29: J4.18 (GPIO_44), U2.50 (PIO0_29/_DACOUT_1)
/PIO0_30: J4.16 (GPIO_42), U2.54 (PIO0_30/ACMP_I5)
/PIO0_31: J3.17 (GPIO_10), U2.13 (PIO0_31/CAPT_X0)
/PIO1_0: J3.19 (GPIO_12), U2.15 (PIO1_0/CAPT_X1)
/PIO1_1: J3.24 (GPIO_15), U2.18 (PIO1_1/CAPT_X2)
/PIO1_2: J3.26 (GPIO_17), U2.20 (PIO1_2/CAPT_X3)
/PIO1_3: J3.33 (GPIO_24), U2.29 (PIO1_3/CAPT_X4)
/PIO1_4: J3.35 (GPIO_26), U2.31 (PIO1_4/CAPT_X5)
/PIO1_5: J4.29 (GPIO_55), U2.35 (PIO1_5/CAPT_X6)
/PIO1_6: J4.28 (GPIO_52), U2.38 (PIO1_6/CAPT_X7)
/PIO1_7: J4.19 (VSS), U2.47 (PIO1_7/CAPT_X8)
/PIO1_8: J3.7 (GPIO_00), U2.1 (PIO1_8/CAPT_YL)
/PIO1_9: J3.9 (GPIO_02), U2.3 (PIO1_9/CAPT_YH)
/PIO1_10: J4.6 (GPIO_32), U2.64 (PIO1_10)
/PIO1_11: J4.8 (GPIO_34), U2.62 (PIO1_11)
/PIO1_12: J3.13 (GPIO_06), U2.9 (PIO1_12)
/PIO1_13: J3.15 (GPIO_08), U2.11 (PIO1_13)
/PIO1_14: J3.28 (GPIO_19), U2.22 (PIO1_14)
/PIO1_15: J3.30 (GPIO_21), U2.24 (PIO1_15)
/PIO1_16: J4.30 (GPIO_54), U2.36 (PIO1_16)
/PIO1_17: J4.27 (GPIO_53), U2.37 (PIO1_17)
/PIO1_18: J4.25 (GPIO_51), U2.43 (PIO1_18)
/PIO1_19: J4.26 (GPIO_50), U2.44 (PIO1_19)
/PIO1_20: J4.14 (GPIO_40), U2.56 (PIO1_20)
/PIO1_21: J4.9 (GPIO_37), U2.59 (PIO1_21)
/RESET: C14.2, J1.10 (nRESET), JP1.2, R6.1, R13.1, TP5.1, U2.5 (RESET/PIO0_5)
/TCK: J1.4 (SWDCLK/TCK), JP2.2, R3.1, TP2.1, U2.12 (SWCLK/PIO0_3/TCK)
/TDI: J1.8 (TDI), R5.1
/TDO: J1.6 (SWO/TDO), R4.1
/TMS: J1.2 (SWDIO/TMS), JP3.2, R2.1, TP1.1, U2.14 (SWDIO/PIO0_2/TMS)
/VBUS: C2.2, F1.1, J3.3 (VBUS), J3.4 (VBUS), U1.2 (Vin)
/VDD: C1.1, C5.1, C6.1, C7.1, C8.1, C15.1, C16.1, FB4.2, J1.1 (VCC), J3.1 (VDD), J3.2 (VDD), J4.1 (VSS), J4.2 (VSS), R2.2, R4.2, R5.2, R6.2, R8.2, R14.2, U1.3 (Vout), U2.7 (VDD), U2.26 (VDD), U2.39 (VDD)
/VDDA: C11.1, C13.1, FB4.1, JP4.1, U2.52 (VDDA)
/VREFN: C10.2, C12.2, JP5.2, U2.41 (VREFN)
/VREFP: C10.1, C12.1, JP4.2, U2.42 (VREFP)
/VSS: C1.2, C2.1, C3.2, C4.2, C5.2, C6.2, C7.2, C8.2, C9.1, C14.1, C15.2, C16.2, C17.1, D2.1 (K), FB5.2, J1.3 (GND), J1.5 (GND), J1.9 (GNDDET), J2.A1B12 (GND), J2.B1A12 (GND), J3.5 (VSS), J3.6 (VSS), J3.21 (VSS), J3.22 (VSS), J3.39 (VSS), J3.40 (VSS), J4.3 (GPIO_31), J4.4 (GPIO_30), J4.21 (GPIO_47), J4.22 (GPIO_46), J4.39 (VDD), J4.40 (VDD), R1.1, R3.2, R7.1, SW1.1, SW2.1, TP3.1, U1.1 (GND), U2.8 (VSS), U2.25 (VSS), U2.40 (VSS), Y1.2, Y1.4
/VSSA: C11.2, C13.2, FB5.1, JP5.1, U2.53 (VSSA)
/XTALIN: C4.1, JP6.1, Y1.1
/XTALOUT: C3.1, JP7.1, Y1.3
unnamed: C9.2, J2.S (Shield)
unnamed: C17.2, FB1.2, J2.A4B9 (VBUS), J2.B4A9 (VBUS)
unnamed: D2.2 (A), R14.1
unnamed: F1.2, FB1.1
unnamed: J2.A5 (CC1), R7.2
unnamed: J2.A6 (DP1), J2.B6 (DP2)
unnamed: J2.A7 (DN1), J2.B7 (DN2)
unnamed: J2.B5 (CC2), R1.2
unnamed: R13.2, SW1.2
