Squantor/squantorDevelBoards/electronics/nuclone_STM32F030K6/nuclone_STM32F030K6.kicad_pcb

## KiCad design electronics/nuclone_STM32F030K6/nuclone_STM32F030K6.kicad_pcb (2021-12-02)

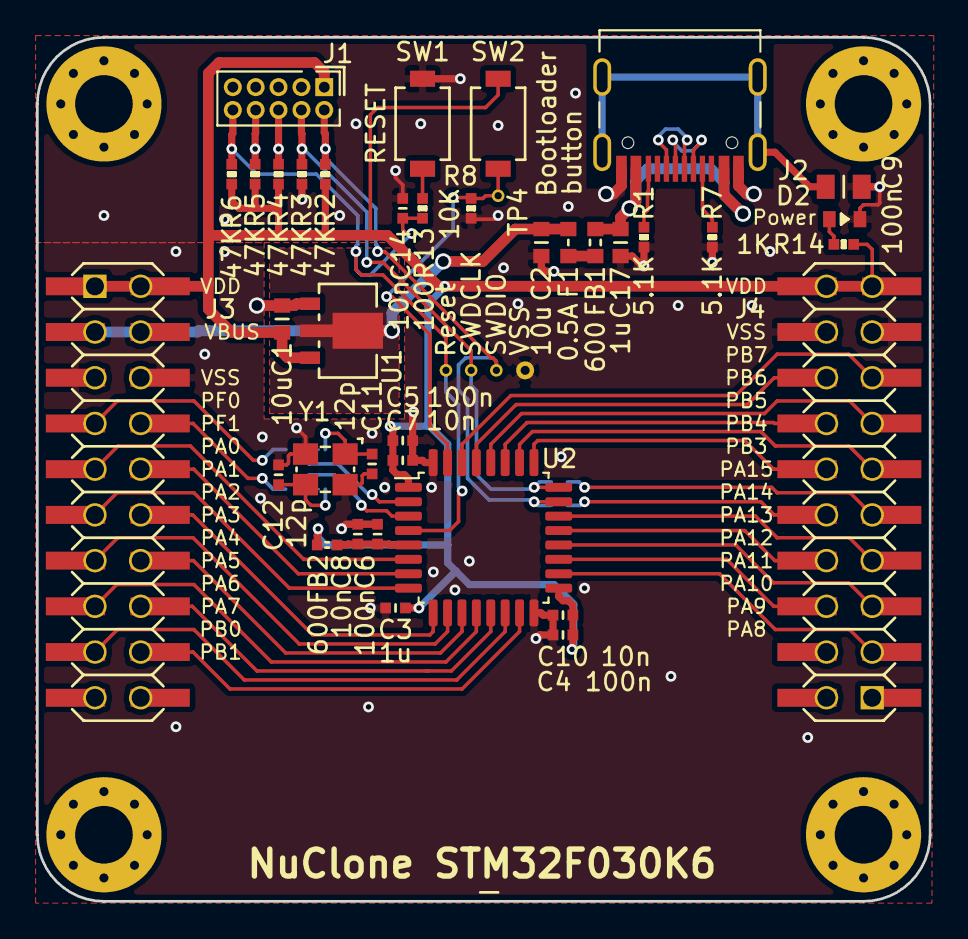
[picture p36: board nuclone_STM32F030K6.kicad_pcb from above]

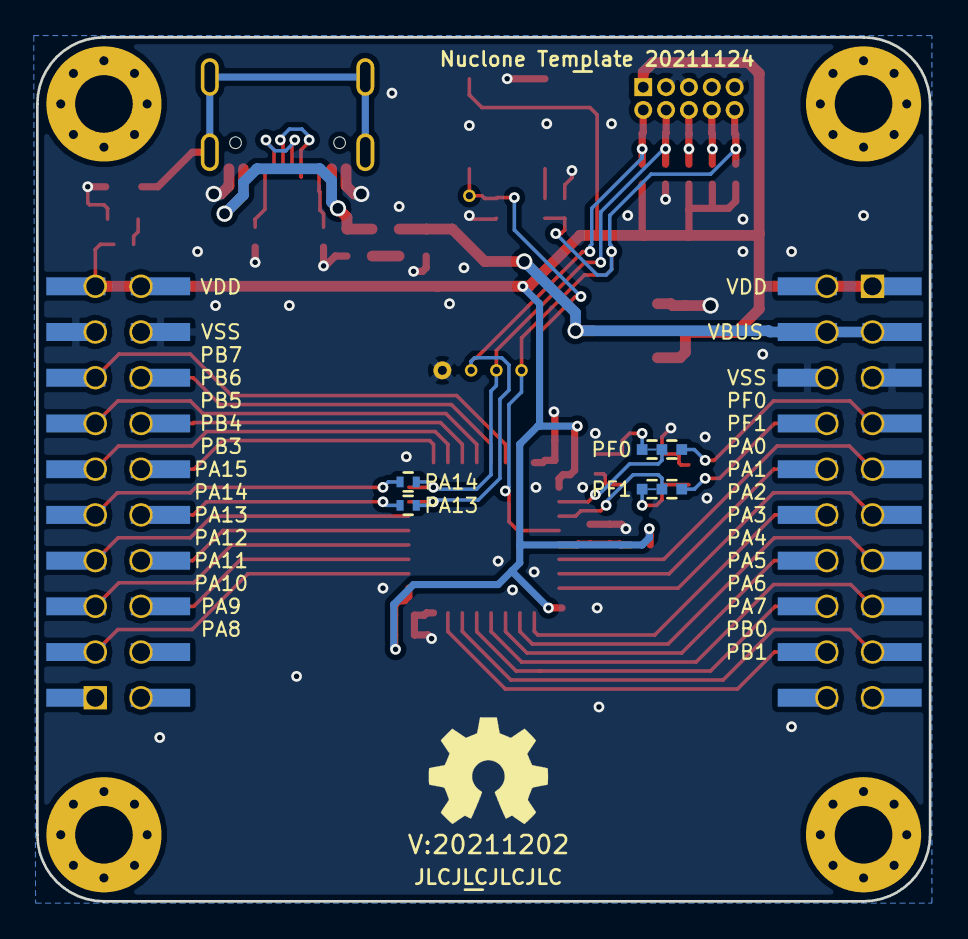
[picture p37: board nuclone_STM32F030K6.kicad_pcb from below]

Board: 2 copper layers, 49.6 x 48.0 mm, 55 parts (8 on the bottom side), 48 nets.

Parts:
C1, C2: 10u; C_0603
C3: 1u; C_0402
C4, C5, C6: 100n; C_0402
C7, C8, C10, C14: 10n; C_0402
C9: 100n; C_0805
C11, C12: 12p; C_0402
C17: 1u; C_0603
D2: GREEN; LED_0603_hand
F1: 0.5A; F_0603_hand
FB1: 600; L_0603
FB2: 600; L_0402
H1, H2, H3, H4: MountingHole; MountingHole_3.2mm_M3_Pad_Via
J1: JTAG_2X05; Header-0127-2X05-H006
J2: TYPE-C-31-M-12; USB-C-HRO-31-M-12
J3: nuclone_small_left; nuclone_small_left_stacked
J4: nuclone_small_right; nuclone_small_right_stacked
JP1: PA13; solder_jumper_2way_noconn
JP2: PA14; solder_jumper_2way_noconn
JP3: PF0; solder_jumper_3way_12conn
JP4: PF1; solder_jumper_3way_12conn
N1: OHWLOGO; OSHW-Symbol_6.7x6mm_SilkScreen
N2: 20211202; Label_version
N3: JLCJLCJLCJLC; Label_Generic
N4: NuClone STM32F030K6; Label_Generic
N5: Nuclone Template 20211124; Label_Generic
R1, R7: 5.1K; R_0402_hand
R2, R3, R4, R5, R6: 47K; R_0402_hand
R8: 10K; R_0402_hand
R13: 100; R_0402_hand
R14: 1K; R_0402_hand
SW1: RESET; TD-85XU
SW2: Bootloader; TD-85XU
TP1: SWDIO; TestPoint_hole_H04R07
TP2: SWDCLK; TestPoint_hole_H04R07
TP3: VSS; TestPoint_hole_H05R10
TP4: button; TestPoint_hole_H04R07
TP5: Reset; TestPoint_hole_H04R07
U1: MCP1702-MB; SOT89-NXP
U2: STM32F030K6; LQFP-32_7x7mm_P0.8mm
Y1: 16MHz; Crystal_3225_4

Connections:
/Bootloader: R8.1, SW2.2, TP4.1, U2.31
/GPIO_00: J3.7, JP3.3
/GPIO_01: J3.8, JP4.3
/GPIO_02: J3.9, U2.6
/GPIO_03: J3.10, U2.7
/GPIO_04: J3.11, U2.8
/GPIO_05: J3.12, U2.9
/GPIO_06: J3.13, U2.10
/GPIO_07: J3.14, U2.11
/GPIO_08: J3.15, U2.12
/GPIO_09: J3.16, U2.13
/GPIO_10: J3.17, U2.14
/GPIO_11: J3.18, U2.15
/GPIO_17: J4.3, U2.18
/GPIO_18: J4.6, U2.19
/GPIO_19: J4.5, U2.20
/GPIO_20: J4.8, U2.21
/GPIO_21: J4.7, U2.22
/GPIO_22: J4.10, JP1.1
/GPIO_23: J4.9, JP2.1
/GPIO_24: J4.12, U2.25
/GPIO_25: J4.11, U2.26
/GPIO_26: J4.14, U2.27
/GPIO_27: J4.13, U2.28
/GPIO_28: J4.16, U2.29
/GPIO_29: J4.15, U2.30
/RESET: C14.2, J1.10, R6.1, R13.1, TP5.1, U2.4
/TCK: J1.4, JP2.2, R3.1, TP2.1, U2.24
/TDI: J1.8, R5.1
/TDO: J1.6, R4.1
/TMS: J1.2, JP1.2, R2.1, TP1.1, U2.23
/VBUS: C2.2, F1.1, J3.3, J3.4, U1.2
/VDD: C1.1, C3.1, C4.1, C5.1, C7.1, C10.1, FB2.2, J1.1, J3.1, J3.2, J4.19, J4.20, R2.2, R4.2, R5.2, R6.2, R14.2, SW2.1, U1.3, U2.1, U2.17
/VSS: C1.2, C2.1, C3.2, C4.2, C5.2, C6.2, C7.2, C8.2, C9.1, C10.2, C11.2, C12.2, C14.1, C17.1, D2.1, J1.3, J1.5, J1.9, J2.A1B12, J2.B1A12, J3.5, J3.6, J4.17, J4.18, R1.1, R3.2, R7.1, R8.2, SW1.1, TP3.1, U1.1, U2.16, U2.32, Y1.2, Y1.4
/microcontroller/OSCIN: JP3.2, U2.2
/microcontroller/OSCOUT: JP4.2, U2.3
/microcontroller/VDDA: C6.1, C8.1, FB2.1, U2.5
unnamed: C9.2, J2.S
unnamed: C11.1, JP3.1, Y1.1
unnamed: C12.1, JP4.1, Y1.3
unnamed: C17.2, FB1.2, J2.A4B9, J2.B4A9
unnamed: D2.2, R14.1
unnamed: F1.2, FB1.1
unnamed: J2.A5, R7.2
unnamed: J2.A6, J2.B6
unnamed: J2.A7, J2.B7
unnamed: J2.B5, R1.2
unnamed: R13.2, SW1.2
