Squantor/squantorDevelBoards/electronics/nuclone_STM32F030C8T6/nuclone_STM32F030C8T6.kicad_pcb

## KiCad design electronics/nuclone_STM32F030C8T6/nuclone_STM32F030C8T6.kicad_pcb (2021-12-02)

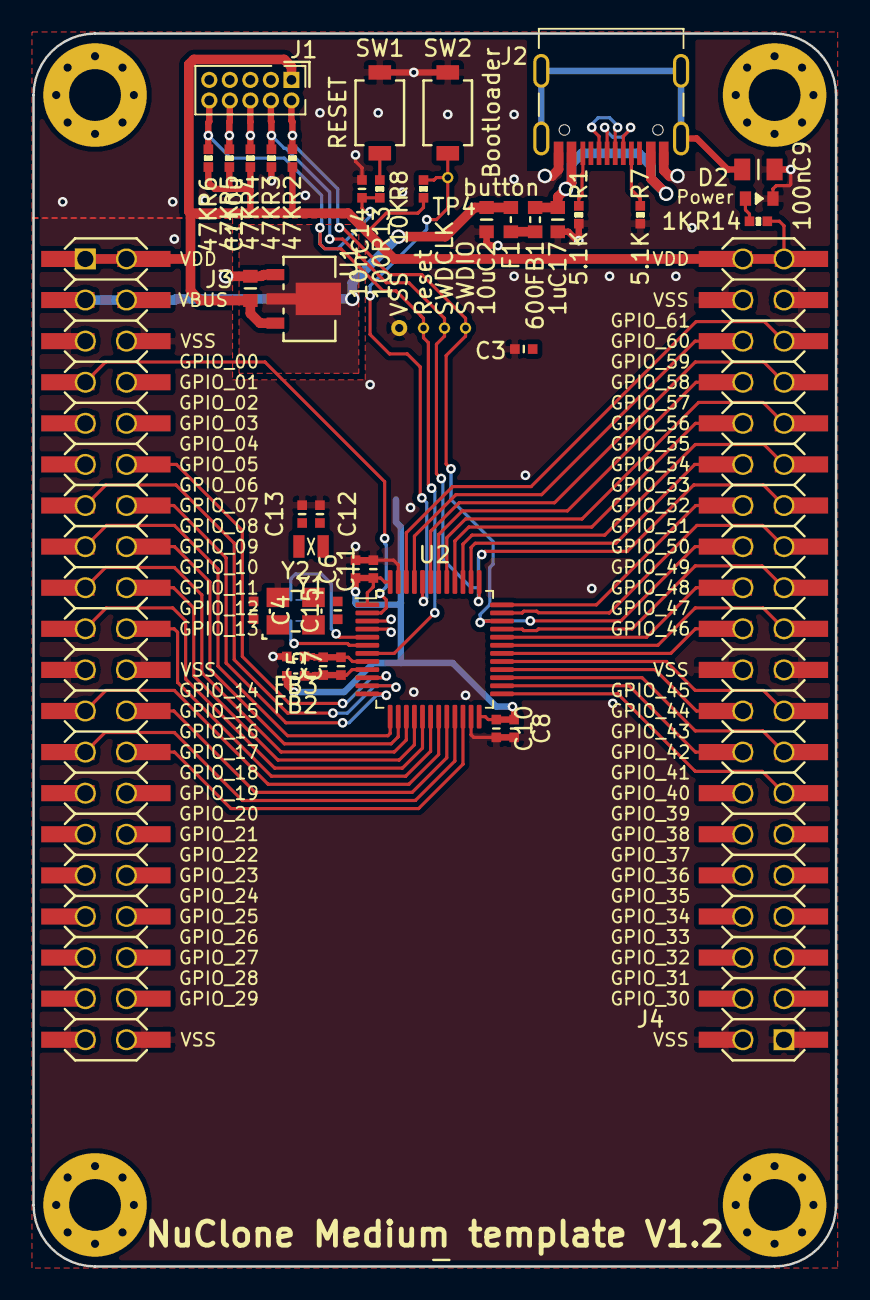
[picture p38: board nuclone_STM32F030C8T6.kicad_pcb from above]

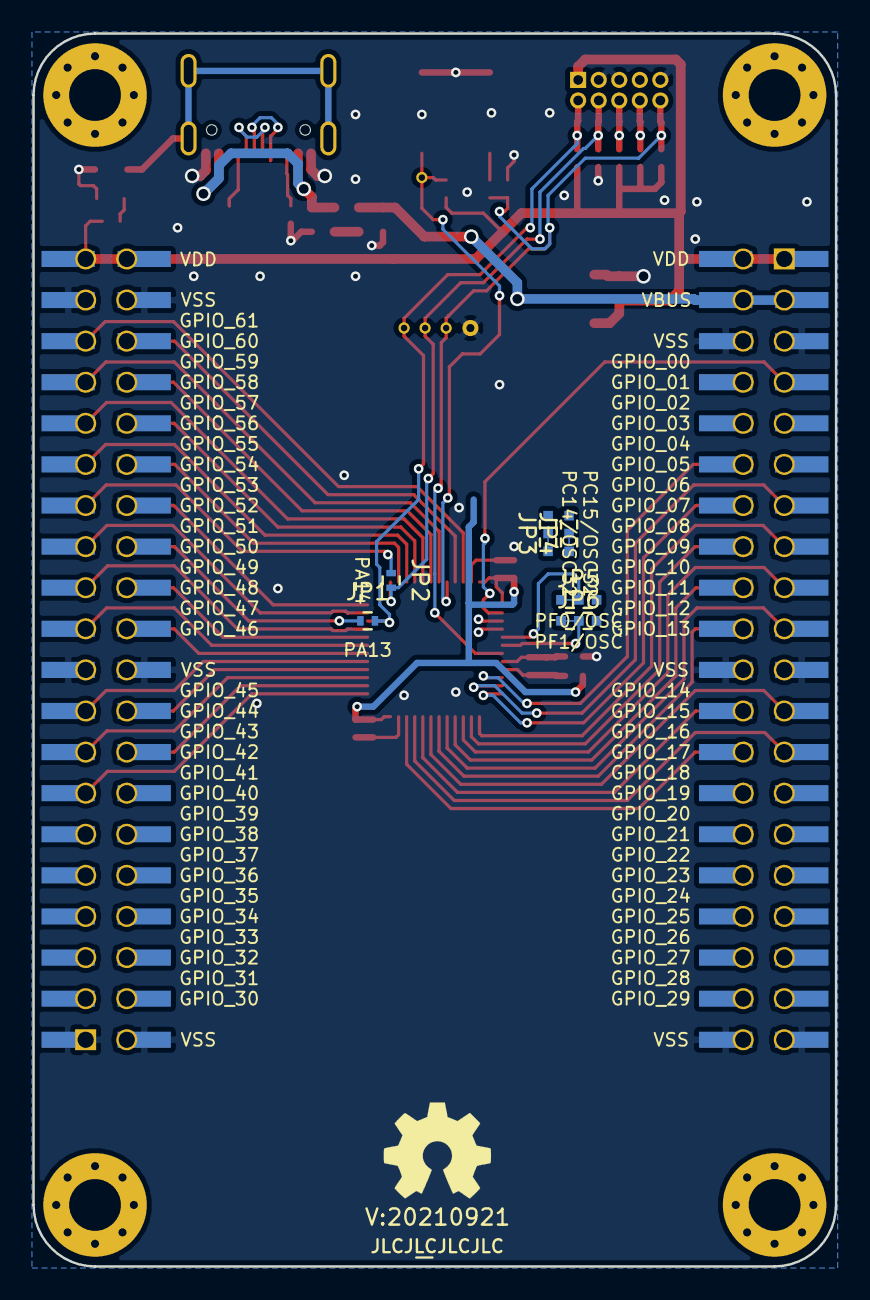
[picture p39: board nuclone_STM32F030C8T6.kicad_pcb from below]

Board: 2 copper layers, 49.6 x 76.2 mm, 60 parts (9 on the bottom side), 67 nets.

Parts:
C1, C2: 10u; C_0603
C3: 1u; C_0402
C4, C12, C13, C15: 10p; C_0402
C5, C6, C8: 100n; C_0402
C7, C10, C11, C14: 10n; C_0402
C9: 100n; C_0805
C17: 1u; C_0603
D2: GREEN; LED_0603_hand
F1: 0.5A; F_0603_hand
FB1: 600; L_0603
FB2, FB3: 600; L_0402
H1, H2, H3, H4: MountingHole; MountingHole_3.2mm_M3_Pad_Via
J1: JTAG_2X05; Header-0127-2X05-H006
J2: TYPE-C-31-M-12; USB-C-HRO-31-M-12
J3: nuclone_medium_left; nuclone_medium_left_stacked
J4: nuclone_medium_right; nuclone_medium_right_stacked
JP1: PA13; solder_jumper_2way_noconn
JP2: PA14; solder_jumper_2way_noconn
JP3: PC14/OSC32; solder_jumper_3way_12conn
JP4: PC15/OSC32; solder_jumper_3way_12conn
JP5: PF0/OSC; solder_jumper_3way_12conn
JP6: PF1/OSC; solder_jumper_3way_12conn
N1: OHWLOGO; OSHW-Symbol_6.7x6mm_SilkScreen
N2: 20210921; Label_version
N3: JLCJLCJLCJLC; Label_Generic
N4: NuClone Medium template V1.2; Label_Generic
R1, R7: 5.1K; R_0402_hand
R2, R3, R4, R5, R6: 47K; R_0402_hand
R8: 10K; R_0402_hand
R13: 100; R_0402_hand
R14: 1K; R_0402_hand
SW1: RESET; TD-85XU
SW2: Bootloader; TD-85XU
TP1: SWDIO; TestPoint_hole_H04R07
TP2: SWDCLK; TestPoint_hole_H04R07
TP3: VSS; TestPoint_hole_H05R10
TP4: button; TestPoint_hole_H04R07
TP5: Reset; TestPoint_hole_H04R07
U1: MCP1702-MB; SOT89-NXP
U2: STM32F030C8T6; LQFP-48_7x7mm_P0.5mm
Y1: 32KHz; Crystal_2012_2
Y2: 16MHz; Crystal_3225_4

Connections:
/Bootloader: R8.1, SW2.2, TP4.1, U2.44
/GPIO_00: J3.7, U2.2
/GPIO_01: J3.8, JP3.3
/GPIO_02: J3.9, JP4.3
/GPIO_03: J3.10, JP5.3
/GPIO_04: J3.11, JP6.3
/GPIO_05: J3.12, U2.10
/GPIO_06: J3.13, U2.11
/GPIO_07: J3.14, U2.12
/GPIO_08: J3.15, U2.13
/GPIO_09: J3.16, U2.14
/GPIO_10: J3.17, U2.15
/GPIO_11: J3.18, U2.16
/GPIO_12: J3.19, U2.17
/GPIO_13: J3.20, U2.18
/GPIO_14: J3.23, U2.19
/GPIO_15: J3.24, U2.20
/GPIO_16: J3.25, U2.21
/GPIO_17: J3.26, U2.22
/GPIO_41: J4.13, U2.25
/GPIO_42: J4.16, U2.26
/GPIO_43: J4.15, U2.27
/GPIO_44: J4.18, U2.28
/GPIO_45: J4.17, U2.29
/GPIO_46: J4.22, U2.30
/GPIO_47: J4.21, U2.31
/GPIO_48: J4.24, U2.32
/GPIO_49: J4.23, U2.33
/GPIO_50: J4.26, JP1.1
/GPIO_51: J4.25, U2.35
/GPIO_52: J4.28, U2.36
/GPIO_53: J4.27, JP2.1
/GPIO_54: J4.30, U2.38
/GPIO_55: J4.29, U2.39
/GPIO_56: J4.32, U2.40
/GPIO_57: J4.31, U2.41
/GPIO_58: J4.34, U2.42
/GPIO_59: J4.33, U2.43
/GPIO_60: J4.36, U2.45
/GPIO_61: J4.35, U2.46
/RESET: C14.2, J1.10, R6.1, R13.1, TP5.1, U2.7
/TCK: J1.4, JP2.2, R3.1, TP2.1, U2.37
/TDI: J1.8, R5.1
/TDO: J1.6, R4.1
/TMS: J1.2, JP1.2, R2.1, TP1.1, U2.34
/VBUS: C2.2, F1.1, J3.3, J3.4, U1.2
/VDD: C1.1, C3.1, C6.1, C8.1, C10.1, C11.1, FB2.2, J1.1, J3.1, J3.2, J4.39, J4.40, R2.2, R4.2, R5.2, R6.2, R8.2, R14.2, U1.3, U2.1, U2.24, U2.48
/VSS: C1.2, C2.1, C3.2, C4.1, C6.2, C8.2, C9.1, C10.2, C11.2, C12.1, C13.2, C14.1, C15.1, C17.1, D2.1, FB3.2, J1.3, J1.5, J1.9, J2.A1B12, J2.B1A12, J3.5, J3.6, J3.21, J3.22, J3.39, J3.40, J4.1, J4.2, J4.19, J4.20, J4.37, J4.38, R1.1, R3.2, R7.1, SW1.1, SW2.1, TP3.1, U1.1, U2.23, U2.47, Y2.2, Y2.4
/microcontroller/OSC32IN: C12.2, JP3.1, Y1.1
/microcontroller/OSC32IN_MCU: JP3.2, U2.3
/microcontroller/OSC32OUT: C13.1, JP4.1, Y1.2
/microcontroller/OSC32OUT_MCU: JP4.2, U2.4
/microcontroller/OSCIN: C4.2, JP5.1, Y2.1
/microcontroller/OSCIN_MCU: JP5.2, U2.5
/microcontroller/OSCOUT: C15.2, JP6.1, Y2.3
/microcontroller/OSCOUT_MCU: JP6.2, U2.6
/microcontroller/VDDA: C5.1, C7.1, FB2.1, U2.9
/microcontroller/VSSA: C5.2, C7.2, FB3.1, U2.8
unnamed: C9.2, J2.S
unnamed: C17.2, FB1.2, J2.A4B9, J2.B4A9
unnamed: D2.2, R14.1
unnamed: F1.2, FB1.1
unnamed: J2.A5, R7.2
unnamed: J2.A6, J2.B6
unnamed: J2.A7, J2.B7
unnamed: J2.B5, R1.2
unnamed: R13.2, SW1.2
