Squantor/squantorDevelBoards/electronics/nuclone_LPC824M201JHI33_expansion_microSD_card/nuclone_LPC824M201JHI33_expansion_microSD_card.kicad_pcb

## KiCad design electronics/nuclone_LPC824M201JHI33_expansion_microSD_card/nuclone_LPC824M201JHI33_expansion_microSD_card.kicad_pcb (2020-11-08)

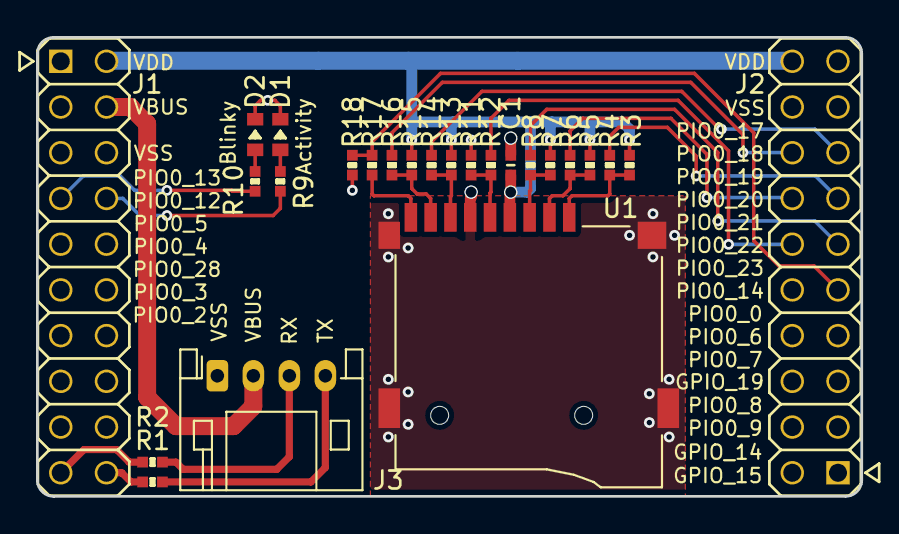
[picture p40: board nuclone_LPC824M201JHI33_expansion_microSD_card.kicad_pcb from above]

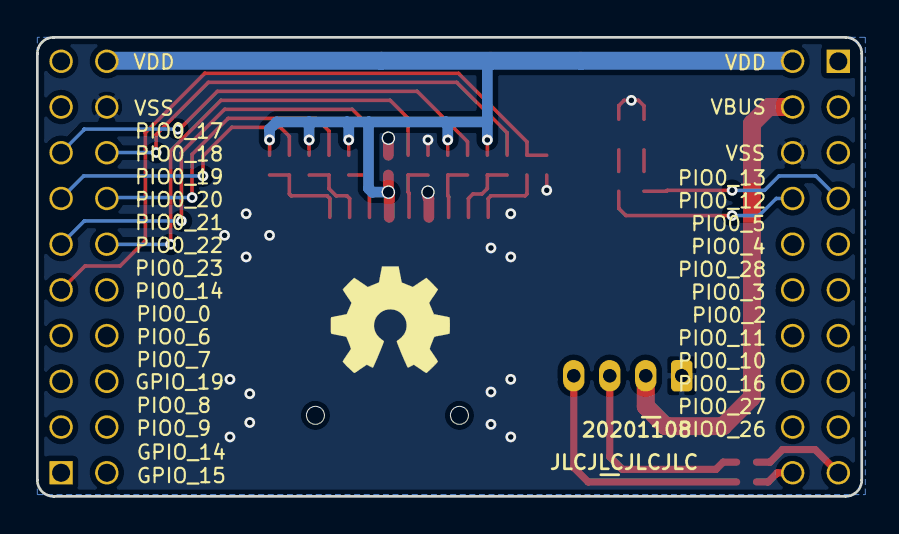
[picture p41: board nuclone_LPC824M201JHI33_expansion_microSD_card.kicad_pcb from below]

Board: 2 copper layers, 45.8 x 25.5 mm, 28 parts (3 on the bottom side), 25 nets.

Parts:
C1: 1u; C_0402
D1, D2: LED; LED_0603_hand
J1: nuclone_small_left; Header-0254-2X10-H010
J2: nuclone_small_right; Header-0254-2X10-H010
J3: DevBoardUartInput; JST_PH_S4B-PH-K_1x04_P2.00mm_Horizontal
N1: OHWLOGO; OSHW-Symbol_6.7x6mm_SilkScreen
N2: 20201108; Label_Generic
N3: JLCJLCJLCJLC; Label_Generic
R1, R2, R4, R6, R8, R12, R14, R16, R17: 100; R_0402_hand
R3, R5, R7, R11, R13, R15: 10k; R_0402_hand
R9, R10: 4.7K; R_0402_hand
R18: 100k; R_0402_hand
U1: microSD_socket; SDmicro_XUNPU_TF-115

Connections:
/CLK: J2.12, R12.2
/CMD: J2.11, R8.2
/CardDet: J2.9, R17.2, R18.2
/DAT0: J2.15, R14.2
/DAT1: J2.16, R16.2
/DAT2: J2.13, R4.2
/DAT3: J2.14, R6.2
/LED0: J1.8, R9.2
/LED1: J1.7, R10.2
/UART_RX: J1.19, R1.1
/UART_TX: J1.20, R2.1
/VBUS: J1.4, J3.2
/VDD: C1.1, J1.1, J1.2, J2.20, R3.2, R5.2, R7.2, R13.2, R15.2, U1.4
/VSS: C1.2, D1.1, D2.1, J1.6, J2.18, J3.1, R11.2, R18.1, U1.6, U1.S
unnamed: D1.2, R9.1
unnamed: D2.2, R10.1
unnamed: J3.3, R1.2
unnamed: J3.4, R2.2
unnamed: R3.1, R4.1, U1.1
unnamed: R5.1, R6.1, U1.2
unnamed: R7.1, R8.1, U1.3
unnamed: R11.1, R12.1, U1.5
unnamed: R13.1, R14.1, U1.7
unnamed: R15.1, R16.1, U1.8
unnamed: R17.1, U1.CD
