Squantor/squantorDevelBoards/electronics/nuclone_LPC824M201JHI33_expansion_wearable/nuclone_LPC824M201JHI33_expansion_wearable.kicad_pcb

## KiCad design electronics/nuclone_LPC824M201JHI33_expansion_wearable/nuclone_LPC824M201JHI33_expansion_wearable.kicad_pcb (2020-09-11)

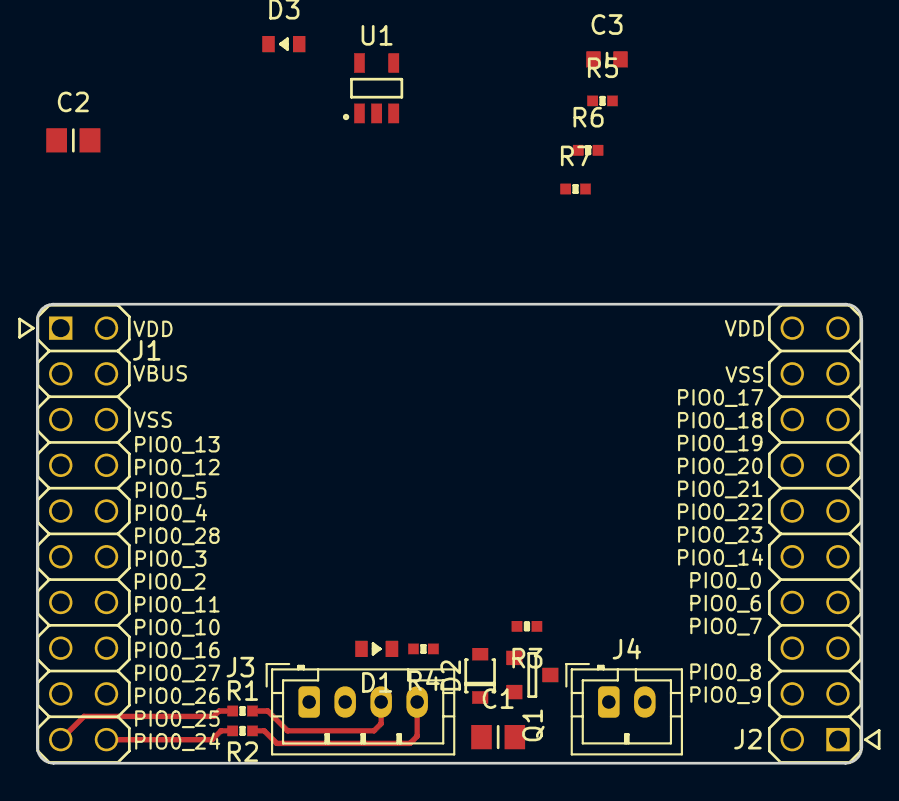
[picture p44: board nuclone_LPC824M201JHI33_expansion_wearable.kicad_pcb from above]

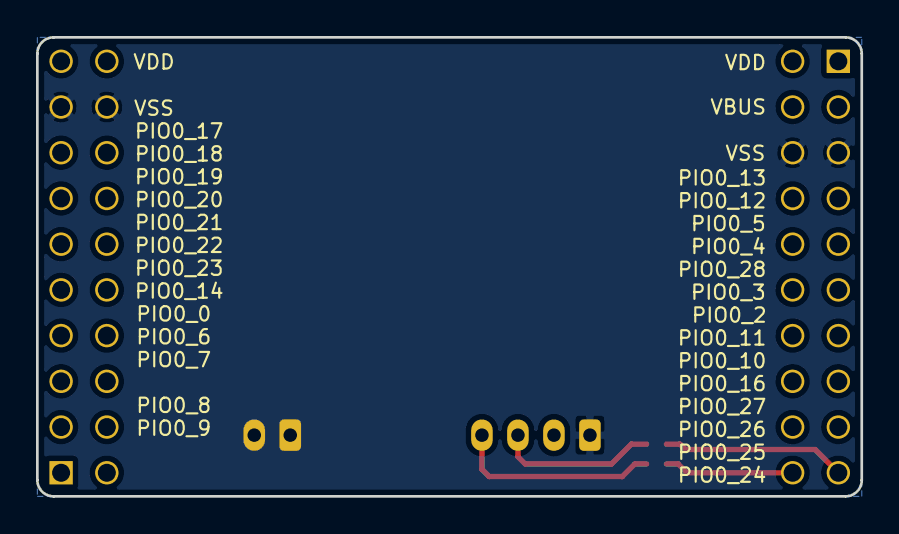
[picture p45: board nuclone_LPC824M201JHI33_expansion_wearable.kicad_pcb from below]

Board: 2 copper layers, 45.8 x 25.5 mm, 22 parts (3 on the bottom side), 13 nets.

Parts:
C1, C2: 10u; C_0805+0603
C3: 1u; C_0603
D1: GRN; LED_0603_hand
D2: NSR0320; SOD_323_onsemi
D3: RED; LED_0603_hand
J1: nuclone_small_left; Header-0254-2X10-H010
J2: nuclone_small_right; Header-0254-2X10-H010
J3: DevBoardUartInput; JST_PH_B4B-PH-K_1x04_P2.00mm_Vertical
J4: batt_recharge; JST_PH_B2B-PH-K_1x02_P2.00mm_Vertical
N1: OHWLOGO; OSHW-Symbol_6.7x6mm_SilkScreen
N2: 20200910; Label_Generic
N3: JLCJLCJLCJLC; Label_Generic
Q1: DMG2305; SOT23-3
R1, R2: 100; R_0402_hand
R3: 100K; R_0402_hand
R4, R6: 1K; R_0402_hand
R5: 22K; R_0402_hand
R7: 47K; R_0402_hand
U1: MCP738312-OT; SOT23-5-Microchip-OT

Connections:
/PIO0_24: J1.20, R2.1
/PIO0_25: J1.19, R1.1
/VBAT: C2.1, J4.1, Q1.3, U1.3
/VBUS: C1.1, D2.1, J1.3, J1.4, Q1.2
/VDD: J1.1, J1.2, J2.19, J2.20, R7.2
/VSS: C1.2, C2.2, C3.1, J1.5, J1.6, J2.17, J2.18, J3.1, J4.2, R3.1, R4.1, R5.2, U1.2
/VUSB: C3.2, D1.2, D2.2, D3.2, J3.2, Q1.1, R3.2, U1.4
/chrg_en: R5.1, U1.5
/chrg_state: R6.1, R7.1, U1.1
unnamed: D1.1, R4.2
unnamed: D3.1, R6.2
unnamed: J3.3, R1.2
unnamed: J3.4, R2.2
