Squantor/squantorDevelBoards/electronics/nuclone_LPC1125JBD48-303/nuclone_LPC1125JBD48-303.kicad_pcb

## KiCad design electronics/nuclone_LPC1125JBD48-303/nuclone_LPC1125JBD48-303.kicad_pcb (2020-01-12)

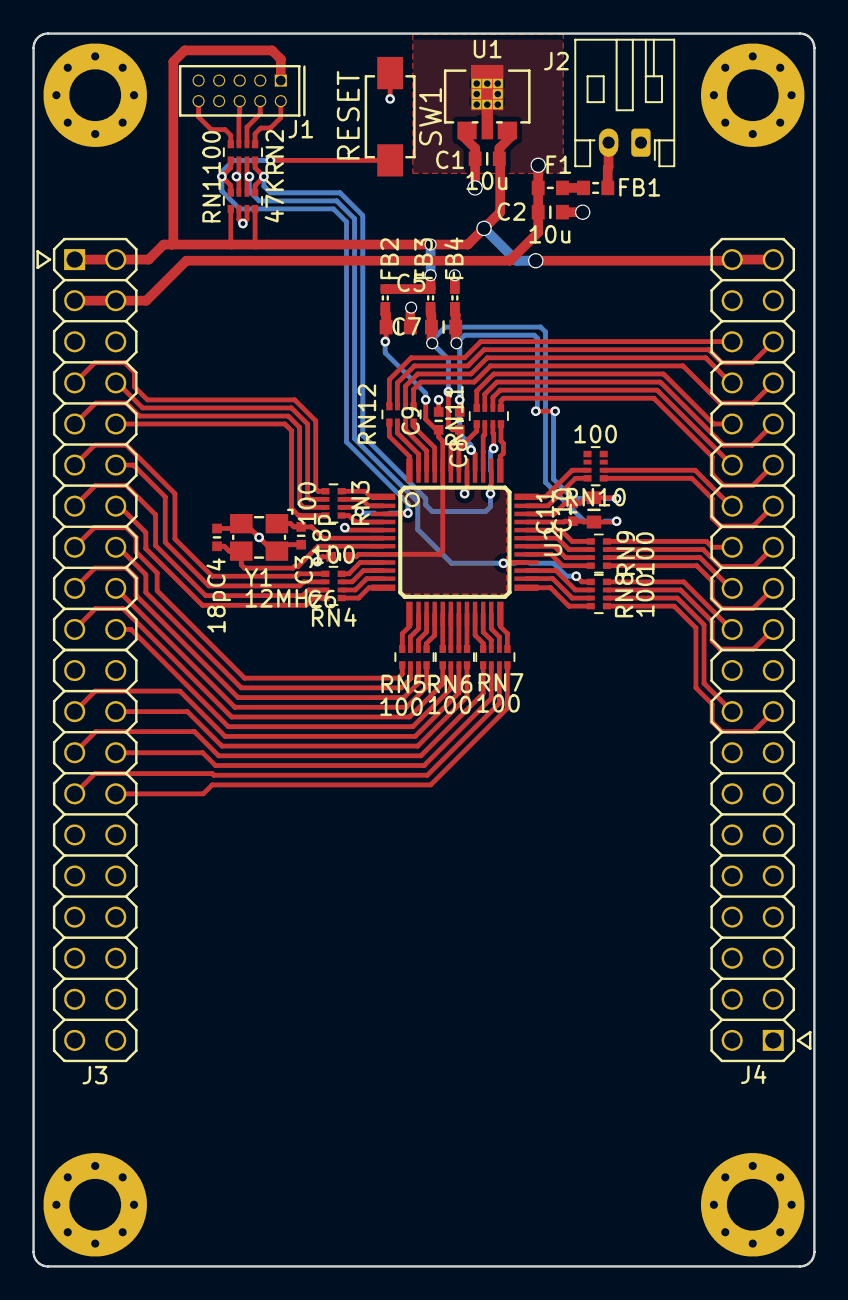
[picture p46: board nuclone_LPC1125JBD48-303.kicad_pcb from above]

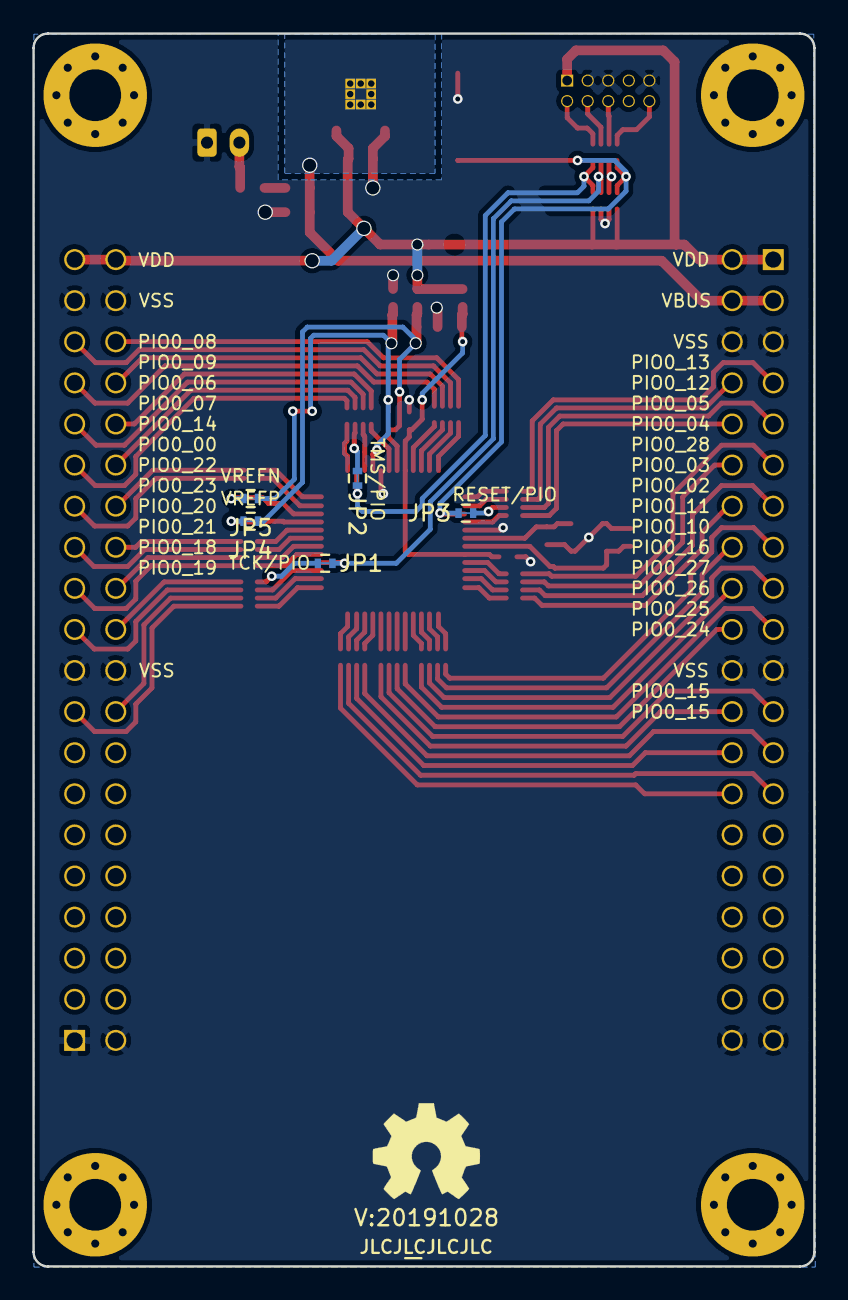
[picture p47: board nuclone_LPC1125JBD48-303.kicad_pcb from below]

Board: 2 copper layers, 48.3 x 76.2 mm, 48 parts (8 on the bottom side), 96 nets.

Parts:
C1, C2, C5, C7, C10: 10u; C_0603
C3, C4: 18p; C_0402
C6, C8, C9, C11: 1u; C_0402
F1: 0.5A; F_0603_hand
FB1: 100; L_0603
FB2, FB3, FB4: FB; L_0402
H1, H2, H3, H4: MountingHole; MountingHole_3.2mm_M3_Pad_Via
J1: JTAG_2X05; Header-0127-2X05-H006
J2: Conn_01x02; JST_PH_S2B-PH-K_1x02_P2.00mm_Horizontal
J3: nuclone_small_left; nuclone_medium_left
J4: nuclone_small_right; nuclone_medium_right
JP1: TCK/PIO; solder_jumper_2way_conn
JP2: TMS/PIO; solder_jumper_2way_conn
JP3: RESET/PIO; solder_jumper_2way_conn
JP4: VREFP; solder_jumper_2way_conn
JP5: VREFN; solder_jumper_2way_conn
N1: OHWLOGO; OSHW-Symbol_6.7x6mm_SilkScreen
N2: 20191028; Label_version
N3: JLCJLCJLCJLC; Label_Generic
RN1: 47K; R_Array_Convex_4x0402
RN2, RN3, RN4, RN5, RN6, RN7, RN8, RN9, RN10, RN11, RN12: 100; R_Array_Convex_4x0402
SW1: RESET; DTSM3
U1: MCP1702-MB; SOT89-SOT23-Dual-NXP
U2: LPC1125JBD48_303; SOT313-2-NXP
Y1: 12MHz; Crystal_3225_4

Connections:
/PIO0_0: JP3.1, RN3.2
/PIO0_0_MCU: JP3.2, RN1.8, RN2.5, SW1.2, U2.3
/PIO0_0_OUT: J3.9, RN3.7
/PIO0_1_MCU: RN3.1, U2.4
/PIO0_1_OUT: J3.10, RN3.8
/PIO0_2_MCU: RN4.3, U2.10
/PIO0_2_OUT: J3.12, RN4.6
/PIO0_3_MCU: RN5.3, U2.14
/PIO0_3_OUT: J3.16, RN5.6
/PIO0_4_MCU: RN5.2, U2.15
/PIO0_4_OUT: J3.17, RN5.7
/PIO0_5_MCU: RN5.1, U2.16
/PIO0_5_OUT: J3.18, RN5.8
/PIO0_6_MCU: RN7.3, U2.22
/PIO0_6_OUT: J3.26, RN7.6
/PIO0_7_MCU: RN7.2, U2.23
/PIO0_7_OUT: J3.27, RN7.7
/PIO0_8_MCU: RN8.3, U2.26
/PIO0_8_OUT: J4.18, RN8.6
/PIO0_9_MCU: RN8.2, U2.27
/PIO0_9_OUT: J4.21, RN8.7
/PIO0_10: JP1.1, RN8.1
/PIO0_10_MCU: JP1.2, RN1.6, RN2.7, U2.28
/PIO0_10_OUT: J4.22, RN8.8
/PIO0_11_MCU: RN9.3, U2.30
/PIO0_11_OUT: J4.24, RN9.6
/PIO1_0_MCU: RN9.2, U2.31
/PIO1_0_OUT: J4.25, RN9.7
/PIO1_1_MCU: RN9.1, U2.32
/PIO1_1_OUT: J4.26, RN9.8
/PIO1_2_MCU: RN10.4, U2.35
/PIO1_2_OUT: J4.27, RN10.5
/PIO1_3: JP2.1, RN11.3
/PIO1_3_MCU: JP2.2, RN1.5, RN2.8, U2.38
/PIO1_3_OUT: J4.30, RN11.6
/PIO1_4_MCU: RN11.2, U2.39
/PIO1_4_OUT: J4.31, RN11.7
/PIO1_5_MCU: RN12.4, U2.45
/PIO1_5_OUT: J4.33, RN12.5
/PIO1_6_MCU: RN12.3, U2.46
/PIO1_6_OUT: J4.34, RN12.6
/PIO1_7_MCU: RN12.2, U2.47
/PIO1_7_OUT: J4.35, RN12.7
/PIO1_8_MCU: RN4.4, U2.9
/PIO1_8_OUT: J3.11, RN4.5
/PIO1_9_MCU: RN6.4, U2.17
/PIO1_9_OUT: J3.19, RN6.5
/PIO1_10_MCU: RN9.4, U2.29
/PIO1_10_OUT: J4.23, RN9.5
/PIO1_11_MCU: RN11.1, U2.42
/PIO1_11_OUT: J4.32, RN11.8
/PIO2_0_MCU: RN3.3, U2.2
/PIO2_0_OUT: J3.8, RN3.6
/PIO2_1_MCU: RN5.4, U2.13
/PIO2_1_OUT: J3.15, RN5.5
/PIO2_2_MCU: RN8.4, U2.25
/PIO2_2_OUT: J4.17, RN8.5
/PIO2_3_MCU: RN11.4, U2.37
/PIO2_3_OUT: J4.29, RN11.5
/PIO2_4_MCU: RN6.2, U2.19
/PIO2_4_OUT: J3.23, RN6.7
/PIO2_5_MCU: RN6.1, U2.20
/PIO2_5_OUT: J3.24, RN6.8
/PIO2_6_MCU: RN3.4, U2.1
/PIO2_6_OUT: J3.7, RN3.5
/PIO2_7_MCU: RN4.2, U2.11
/PIO2_7_OUT: J3.13, RN4.7
/PIO2_8_MCU: RN4.1, U2.12
/PIO2_8_OUT: J3.14, RN4.8
/PIO2_9_MCU: RN7.1, U2.24
/PIO2_9_OUT: J3.28, RN7.8
/PIO3_0_MCU: RN10.3, U2.36
/PIO3_0_OUT: J4.28, RN10.6
/PIO3_3_MCU: RN12.1, U2.48
/PIO3_3_OUT: J4.36, RN12.8
/PIO3_4_MCU: RN6.3, U2.18
/PIO3_4_OUT: J3.20, RN6.6
/PIO3_5_MCU: RN7.4, U2.21
/PIO3_5_OUT: J3.25, RN7.5
/SWO_TDO: RN1.7, RN2.6
/VBUS: C2.2, F1.1, J3.3, J3.4, U1.2
/VDD: C1.1, FB2.2, FB3.2, J1.1, J3.1, J3.2, J4.39, J4.40, RN1.1, RN1.4, U1.3
/VDDA_MCU: C7.1, C8.1, FB3.1, JP4.1, U2.43
/VDD_MCU: C5.1, C6.1, C9.1, FB2.1, U2.8, U2.44
/VREFN_MCU: C10.2, C11.2, JP5.2, U2.34
/VREFP_MCU: C10.1, C11.1, JP4.2, U2.33
/VSSA_MCU: C7.2, C8.2, FB4.1, JP5.1, U2.40
/XTAL_IN: C3.1, U2.6, Y1.1
/XTAL_OUT: C4.1, U2.7, Y1.3
unnamed: F1.2, FB1.1
unnamed: FB1.2, J2.2
unnamed: J1.2, RN2.1
unnamed: J1.4, RN2.2
unnamed: J1.6, RN2.3
unnamed: J1.10, RN2.4
VSS: C1.2, C2.1, C3.2, C4.2, C5.2, C6.2, C9.2, FB4.2, J1.3, J1.5, J1.9, J2.1, J3.5, J3.6, J3.21, J3.22, J3.39, J3.40, J4.1, J4.2, J4.19, J4.20, J4.37, J4.38, RN1.2, RN1.3, SW1.1, U1.1, U2.5, U2.41, Y1.2, Y1.4
