Squantor/squantorDevelBoards/electronics/nuclone_tester_medium/nuclone_tester_medium.kicad_pcb

## KiCad design electronics/nuclone_tester_medium/nuclone_tester_medium.kicad_pcb (2020-01-18)

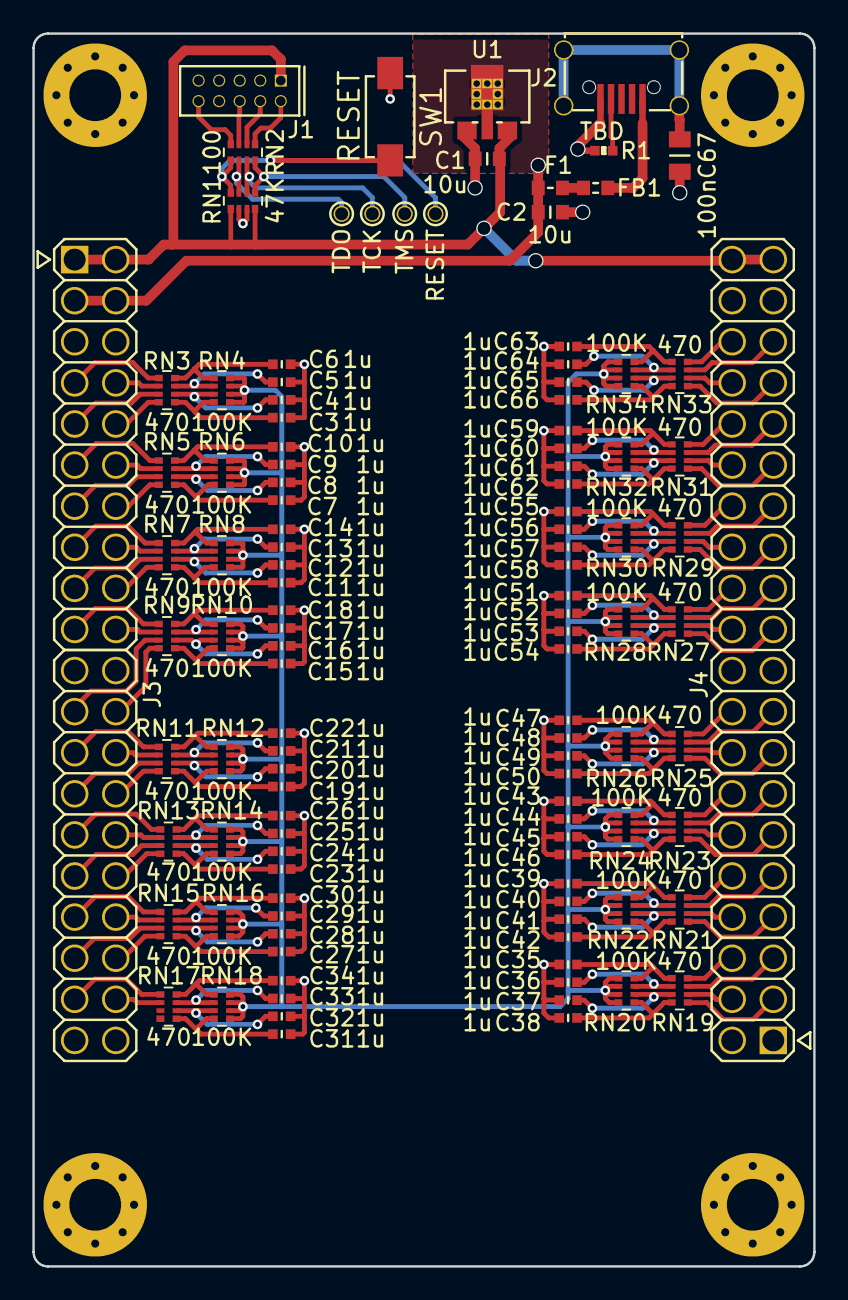
[picture p48: board nuclone_tester_medium.kicad_pcb from above]

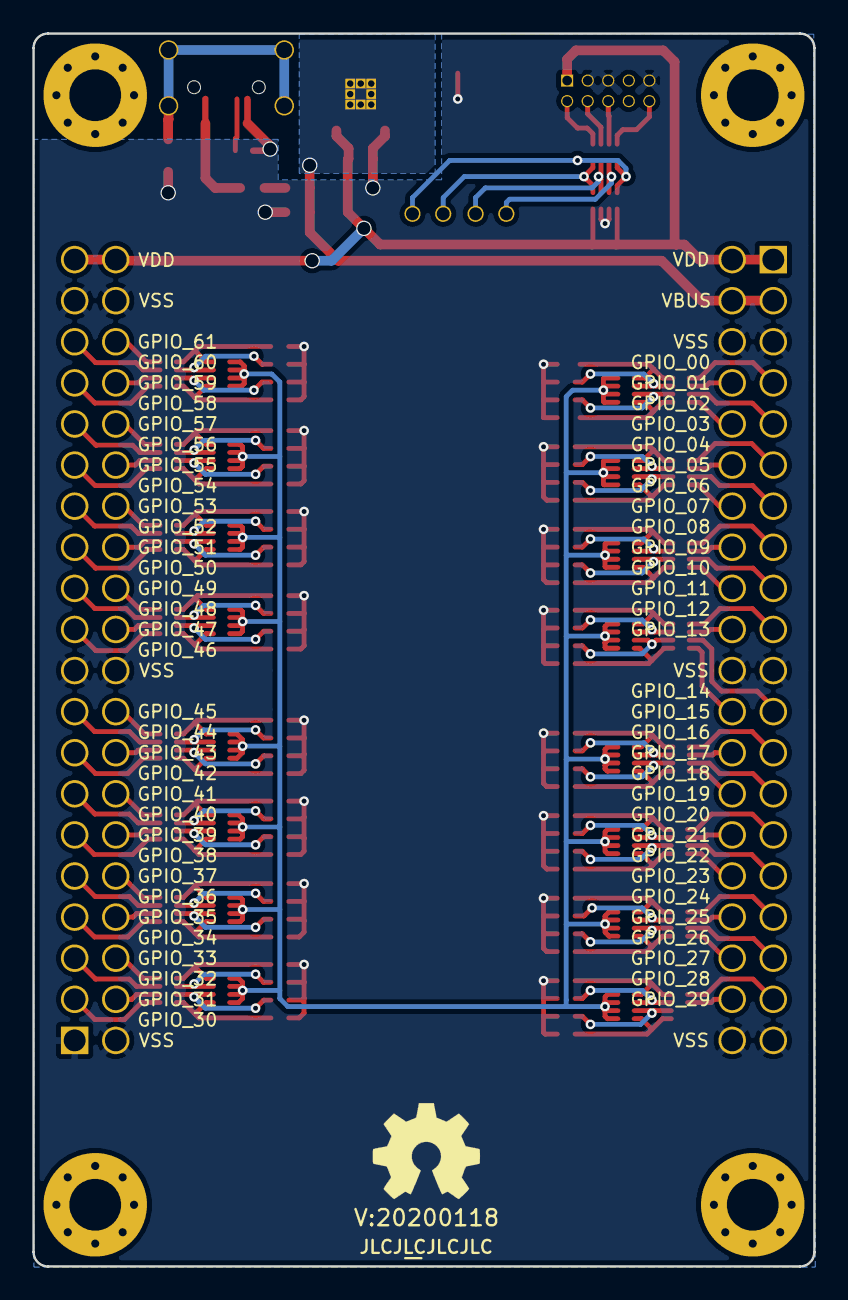
[picture p49: board nuclone_tester_medium.kicad_pcb from below]

Board: 2 copper layers, 48.3 x 76.2 mm, 121 parts (3 on the bottom side), 142 nets.

Parts:
C1, C2: 10u; C_0603
C3, C4, C5, C6, C7, C8, C9, C10, C11, C12, C13, C14, C15, C16, C17, C18, C19, C20, C21, C22, C23, C24, C25, C26, C27, C28, C29, C30, C31, C32, C33, C34, C35, C36, C37, C38, C39, C40, C41, C42, C43, C44, C45, C46, C47, C48, C49, C50, C51, C52, C53, C54, C55, C56, C57, C58, C59, C60, C61, C62, C63, C64, C65, C66: 1u; C_0402
C67: 100n; C_0805
F1: 0.5A; F_0603_hand
FB1: 100; L_0603
H1, H2, H3, H4: MountingHole; MountingHole_3.2mm_M3_Pad_Via
J1: JTAG_2X05; Header-0127-2X05-H006
J2: USB-ID; USB-muB-SMD_TH
J3: nuclone_small_left; nuclone_medium_left_1_35mm
J4: nuclone_small_right; nuclone_medium_right_1_35mm
N1: OHWLOGO; OSHW-Symbol_6.7x6mm_SilkScreen
N2: 20200118; Label_version
N3: JLCJLCJLCJLC; Label_Generic
R1: TBD; R_0402_hand
RN1: 47K; R_Array_Convex_4x0402
RN2: 100; R_Array_Convex_4x0402
RN3, RN5, RN7, RN9, RN11, RN13, RN15, RN17, RN19, RN21, RN23, RN25, RN27, RN29, RN31, RN33: 470; R_Array_Convex_4x0402
RN4, RN6, RN8, RN10, RN12, RN14, RN16, RN18, RN20, RN22, RN24, RN26, RN28, RN30, RN32, RN34: 100K; R_Array_Convex_4x0402
SW1: RESET; DTSM3
TP1: TMS; TestPoint_Hole_D0.8mm
TP2: TCK; TestPoint_Hole_D0.8mm
TP3: TDO; TestPoint_Hole_D0.8mm
TP4: RESET; TestPoint_Hole_D0.8mm
U1: MCP1702-MB; SOT89-SOT23-Dual-NXP

Connections:
/GPIO_00: J3.7, RN3.1
/GPIO_01: J3.8, RN3.2
/GPIO_02: J3.9, RN3.3
/GPIO_03: J3.10, RN3.4
/GPIO_04: J3.11, RN5.1
/GPIO_05: J3.12, RN5.2
/GPIO_06: J3.13, RN5.3
/GPIO_07: J3.14, RN5.4
/GPIO_08: J3.15, RN7.1
/GPIO_09: J3.16, RN7.2
/GPIO_10: J3.17, RN7.3
/GPIO_11: J3.18, RN7.4
/GPIO_12: J3.19, RN9.1
/GPIO_13: J3.20, RN9.2
/GPIO_14: J3.23, RN9.3
/GPIO_15: J3.24, RN9.4
/GPIO_16: J3.25, RN11.1
/GPIO_17: J3.26, RN11.2
/GPIO_18: J3.27, RN11.3
/GPIO_19: J3.28, RN11.4
/GPIO_20: J3.29, RN13.1
/GPIO_21: J3.30, RN13.2
/GPIO_22: J3.31, RN13.3
/GPIO_23: J3.32, RN13.4
/GPIO_24: J3.33, RN15.1
/GPIO_25: J3.34, RN15.2
/GPIO_26: J3.35, RN15.3
/GPIO_27: J3.36, RN15.4
/GPIO_28: J3.37, RN17.1
/GPIO_29: J3.38, RN17.2
/GPIO_30: J4.3, RN19.1
/GPIO_31: J4.4, RN19.2
/GPIO_32: J4.5, RN19.3
/GPIO_33: J4.6, RN19.4
/GPIO_34: J4.7, RN21.1
/GPIO_35: J4.8, RN21.2
/GPIO_36: J4.9, RN21.3
/GPIO_37: J4.10, RN21.4
/GPIO_38: J4.11, RN23.1
/GPIO_39: J4.12, RN23.2
/GPIO_40: J4.13, RN23.3
/GPIO_41: J4.14, RN23.4
/GPIO_42: J4.15, RN25.1
/GPIO_43: J4.16, RN25.2
/GPIO_44: J4.17, RN25.3
/GPIO_45: J4.18, RN25.4
/GPIO_46: J4.21, RN27.1
/GPIO_47: J4.22, RN27.2
/GPIO_48: J4.23, RN27.3
/GPIO_49: J4.24, RN27.4
/GPIO_50: J4.25, RN29.1
/GPIO_51: J4.26, RN29.2
/GPIO_52: J4.27, RN29.3
/GPIO_53: J4.28, RN29.4
/GPIO_54: J4.29, RN31.1
/GPIO_55: J4.30, RN31.2
/GPIO_56: J4.31, RN31.3
/GPIO_57: J4.32, RN31.4
/GPIO_58: J4.33, RN33.1
/GPIO_59: J4.34, RN33.2
/GPIO_60: J4.35, RN33.3
/GPIO_61: J4.36, RN33.4
/PIO0_2_MCU: RN1.5, RN2.8, TP1.1
/PIO0_3_MCU: RN1.6, RN2.7, TP2.1
/PIO0_5_MCU: RN1.8, RN2.5, SW1.2, TP4.1
/SWO_TDO: RN1.7, RN2.6, TP3.1
/Stimulus: RN4.5, RN4.6, RN4.7, RN4.8, RN6.5, RN6.6, RN6.7, RN6.8, RN8.5, RN8.6, RN8.7, RN8.8, RN10.5, RN10.6, RN10.7, RN10.8, RN12.5, RN12.6, RN12.7, RN12.8, RN14.5, RN14.6, RN14.7, RN14.8, RN16.5, RN16.6, RN16.7, RN16.8, RN18.5, RN18.6, RN18.7, RN18.8, RN20.5, RN20.6, RN20.7, RN20.8, RN22.5, RN22.6, RN22.7, RN22.8, RN24.5, RN24.6, RN24.7, RN24.8, RN26.5, RN26.6, RN26.7, RN26.8, RN28.5, RN28.6, RN28.7, RN28.8, RN30.5, RN30.6, RN30.7, RN30.8, RN32.5, RN32.6, RN32.7, RN32.8, RN34.5, RN34.6, RN34.7, RN34.8
/VBUS: C2.2, F1.1, J3.3, J3.4, U1.2
/VDD: C1.1, J1.1, J3.1, J3.2, J4.39, J4.40, RN1.1, RN1.4, U1.3
/VSS: C1.2, C2.1, C3.2, C4.2, C5.2, C6.2, C7.2, C8.2, C9.2, C10.2, C11.2, C12.2, C13.2, C14.2, C15.2, C16.2, C17.2, C18.2, C19.2, C20.2, C21.2, C22.2, C23.2, C24.2, C25.2, C26.2, C27.2, C28.2, C29.2, C30.2, C31.2, C32.2, C33.2, C34.2, C35.2, C36.2, C37.2, C38.2, C39.2, C40.2, C41.2, C42.2, C43.2, C44.2, C45.2, C46.2, C47.2, C48.2, C49.2, C50.2, C51.2, C52.2, C53.2, C54.2, C55.2, C56.2, C57.2, C58.2, C59.2, C60.2, C61.2, C62.2, C63.2, C64.2, C65.2, C66.2, C67.2, J1.3, J1.5, J1.9, J2.5, J3.5, J3.6, J3.21, J3.22, J3.39, J3.40, J4.1, J4.2, J4.19, J4.20, J4.37, J4.38, R1.1, RN1.2, RN1.3, SW1.1, U1.1
unnamed: C3.1, RN3.5, RN4.4
unnamed: C4.1, RN3.6, RN4.3
unnamed: C5.1, RN3.7, RN4.2
unnamed: C6.1, RN3.8, RN4.1
unnamed: C7.1, RN5.5, RN6.4
unnamed: C8.1, RN5.6, RN6.3
unnamed: C9.1, RN5.7, RN6.2
unnamed: C10.1, RN5.8, RN6.1
unnamed: C11.1, RN7.5, RN8.4
unnamed: C12.1, RN7.6, RN8.3
unnamed: C13.1, RN7.7, RN8.2
unnamed: C14.1, RN7.8, RN8.1
unnamed: C15.1, RN9.5, RN10.4
unnamed: C16.1, RN9.6, RN10.3
unnamed: C17.1, RN9.7, RN10.2
unnamed: C18.1, RN9.8, RN10.1
unnamed: C19.1, RN11.5, RN12.4
unnamed: C20.1, RN11.6, RN12.3
unnamed: C21.1, RN11.7, RN12.2
unnamed: C22.1, RN11.8, RN12.1
unnamed: C23.1, RN13.5, RN14.4
unnamed: C24.1, RN13.6, RN14.3
unnamed: C25.1, RN13.7, RN14.2
unnamed: C26.1, RN13.8, RN14.1
unnamed: C27.1, RN15.5, RN16.4
unnamed: C28.1, RN15.6, RN16.3
unnamed: C29.1, RN15.7, RN16.2
unnamed: C30.1, RN15.8, RN16.1
unnamed: C31.1, RN17.5, RN18.4
unnamed: C32.1, RN17.6, RN18.3
unnamed: C33.1, RN17.7, RN18.2
unnamed: C34.1, RN17.8, RN18.1
unnamed: C35.1, RN19.5, RN20.4
unnamed: C36.1, RN19.6, RN20.3
unnamed: C37.1, RN19.7, RN20.2
unnamed: C38.1, RN19.8, RN20.1
unnamed: C39.1, RN21.5, RN22.4
unnamed: C40.1, RN21.6, RN22.3
unnamed: C41.1, RN21.7, RN22.2
unnamed: C42.1, RN21.8, RN22.1
unnamed: C43.1, RN23.5, RN24.4
unnamed: C44.1, RN23.6, RN24.3
unnamed: C45.1, RN23.7, RN24.2
unnamed: C46.1, RN23.8, RN24.1
unnamed: C47.1, RN25.5, RN26.4
unnamed: C48.1, RN25.6, RN26.3
unnamed: C49.1, RN25.7, RN26.2
unnamed: C50.1, RN25.8, RN26.1
unnamed: C51.1, RN27.5, RN28.4
unnamed: C52.1, RN27.6, RN28.3
unnamed: C53.1, RN27.7, RN28.2
unnamed: C54.1, RN27.8, RN28.1
unnamed: C55.1, RN29.5, RN30.4
unnamed: C56.1, RN29.6, RN30.3
unnamed: C57.1, RN29.7, RN30.2
unnamed: C58.1, RN29.8, RN30.1
unnamed: C59.1, RN31.5, RN32.4
unnamed: C60.1, RN31.6, RN32.3
unnamed: C61.1, RN31.7, RN32.2
unnamed: C62.1, RN31.8, RN32.1
unnamed: C63.1, RN33.5, RN34.4
unnamed: C64.1, RN33.6, RN34.3
unnamed: C65.1, RN33.7, RN34.2
unnamed: C66.1, RN33.8, RN34.1
unnamed: C67.1, J2.S
unnamed: F1.2, FB1.1
unnamed: FB1.2, J2.1
unnamed: J1.2, RN2.1
unnamed: J1.4, RN2.2
unnamed: J1.6, RN2.3
unnamed: J1.10, RN2.4
unnamed: J2.4, R1.2
